louislelay/Experimental-Equipment-for-Orthostatic-Exercise/cad/ガイドローラー.sldasm

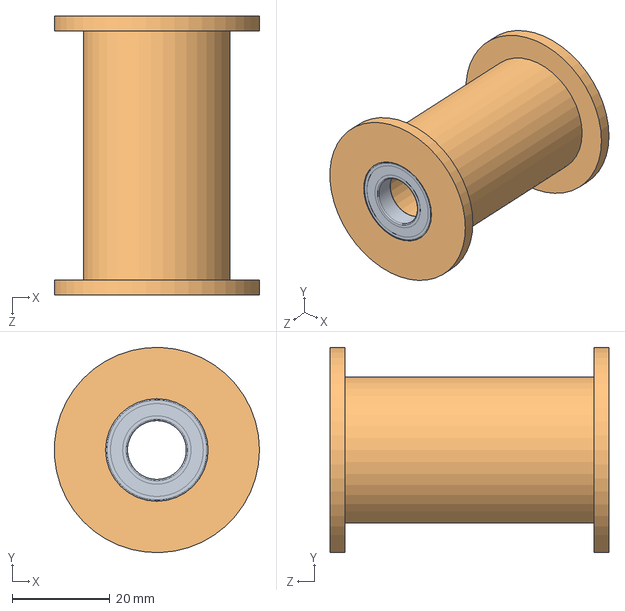
[picture p9: CAD file, 2024-07-01]
cad/ガイドローラー.sldasm
41.9 x 42.0 x 57.0 mm
ガイドローラ_51x30
6801ZZ x 2
