louislelay/Experimental-Equipment-for-Orthostatic-Exercise/cad/ベルト制御ユニット_左.sldasm

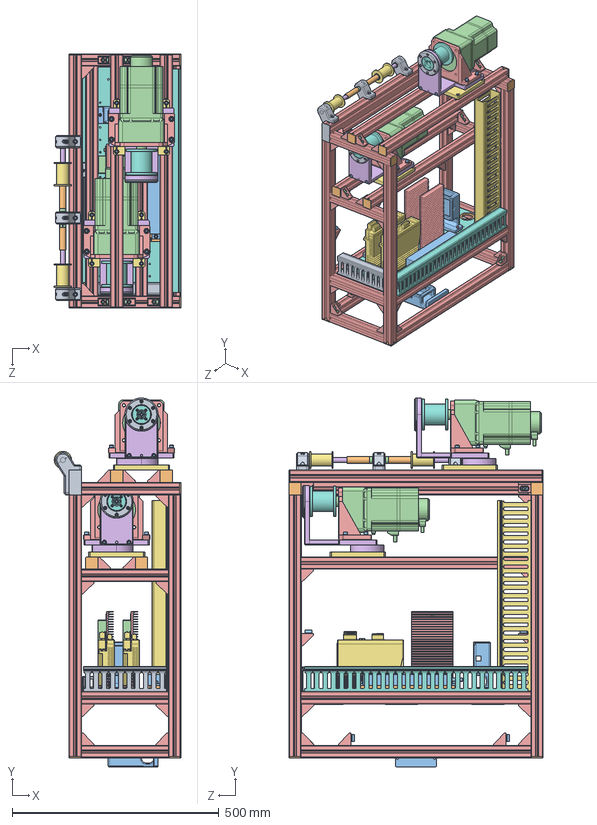
[picture p20: CAD file, 2024-07-01]
cad/ベルト制御ユニット_左.sldasm
306.0 x 892.3 x 615.0 mm
筐体フレーム
配線ダクト用ブラケット x 2
KD-48-20-T
KD-36-20-T
HFC6-3060-B x 2
HFC6-3030-B x 14
HNTP6-6_app x 115
HBLFSN6_CBM6-12 x 98
HBLFSNB6-SEP_b x 49
SFRW12-390-M6-N6_s
ガイドローラ_51x30 x 2
6801ZZ x 4
ガイドローラー用シャフトブラケット x 3
カラー_7 x 2
カラー_30 x 2
カラー_62 x 2
CB6-12 x 29
BXM6200M-10 x 2
SOL6M8 x 2
モーターブラケット x 2
6808ZZ x 2
ベルト巻き取りドラム x 2
ベアリングキャップ x 2
MS6-60 x 2
CB6-20 x 16
WSJ-STN-M6 x 8
CB4-10 x 56
FFS080 v1 x 2
モーターユニット架台プレート x 2
HNTP6-5 x 8
中板
TAP-K4-10用ベース
TAP-K4-10
RGB100 x 2
17F200L100 x 2
抵抗器用ブラケット x 2
BXSD200-A2 x 2
HFB-4001 x 4
KD-36-20-T_200
NAE-032
AIO160802AY-USB用ケース2 x 2
U2H-Z7SBK_用ケース
中板受け用ブラケット x 6
