louislelay/Experimental-Equipment-for-Orthostatic-Exercise/cad/ベルト制御ユニット_右.sldasm

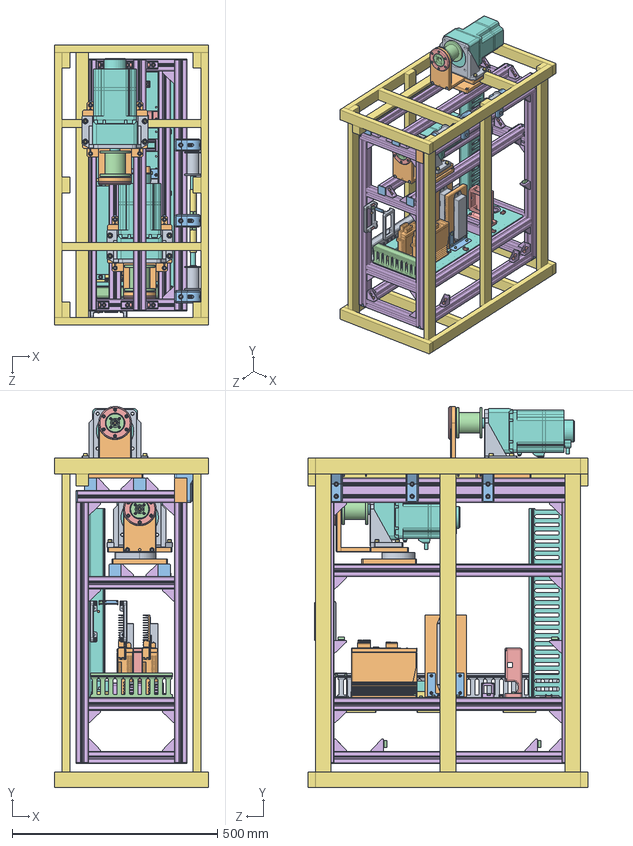
[picture p21: CAD file, 2024-07-01]
cad/ベルト制御ユニット_右.sldasm
376.0 x 928.0 x 683.0 mm
筐体フレーム
配線ダクト用ブラケット x 2
KD-48-20-T
KD-36-20-T
HFC6-3060-B x 2
HFC6-3030-B x 14
HNTP6-6_app x 127
HBLFSN6_CBM6-12 x 98
HBLFSNB6-SEP_b x 49
中板
RGB100 x 2
17F200L100 x 2
抵抗器用ブラケット x 2
CB4-10 x 56
AIO160802AY-USB用ケース2
U2H-Z7SBK_用ケース
TAP-K4-10用ベース
TAP-K4-10
CB6-12 x 41
BXSD200-A2 x 2
HFB-4001 x 4
KD-36-20-T_200
TM2S6-C x 4
NAE-032
中板受け用ブラケット x 6
SFRW12-390-M6-N6_s
ガイドローラ_51x30 x 2
6801ZZ x 4
ガイドローラー用シャフトブラケット x 3
カラー_7 x 2
カラー_2 x 4
カラー_30 x 2
カラー_62 x 2
BXM6200M-10 x 2
SOL6M8 x 2
モーターブラケット x 2
6808ZZ x 2
ベルト巻き取りドラム x 2
ベアリングキャップ x 2
MS6-60 x 2
CB6-20 x 16
WSJ-STN-M6 x 8
FFS080 v1 x 2
モーターユニット架台プレート x 2
HNTP6-5 x 8
ASB-320E x 4
S3B-XH-A
S12B-XH-A
ledverm5mmGa
カバー
