louislelay/Experimental-Equipment-for-Orthostatic-Exercise/cad/USB_IO.SLDASM

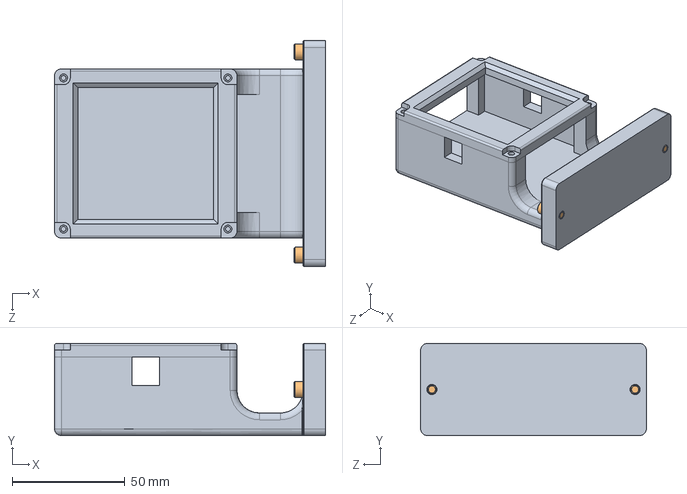
[picture p22: CAD file, 2024-07-01]
cad/USB_IO.SLDASM
120.0 x 40.8 x 100.0 mm
AIO160802AY-USB用ケース2
CB4-10 x 2
