louislelay/Experimental-Equipment-for-Orthostatic-Exercise/cad/hand_protection_pieces/protection hand.SLDPRT

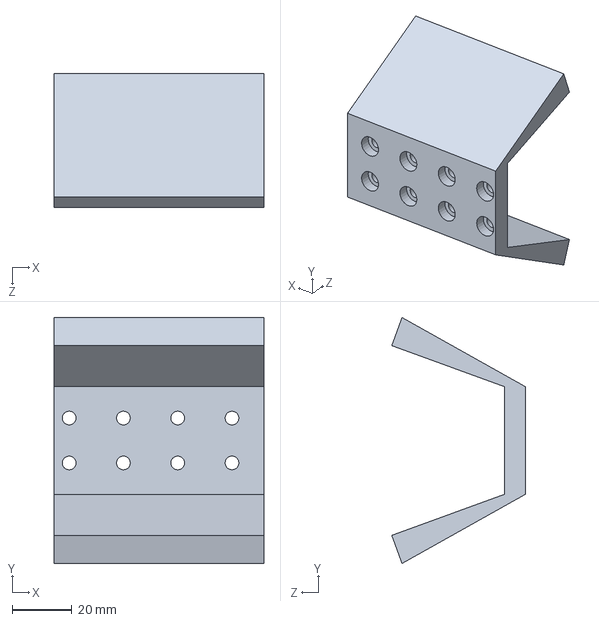
[picture p23: CAD file, 2024-07-02]
cad/hand_protection_pieces/protection hand.SLDPRT
70.0 x 82.2 x 44.6 mm
