louislelay/Experimental-Equipment-for-Orthostatic-Exercise/cad/6808ZZ.SLDPRT

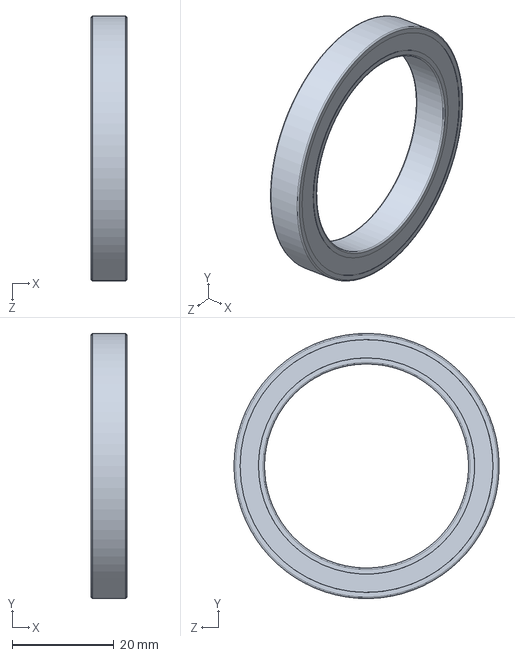
[picture p24: CAD file, 2024-07-01]
cad/6808ZZ.SLDPRT
7.00 x 52.0 x 52.0 mm
