louislelay/Experimental-Equipment-for-Orthostatic-Exercise/cad/hand_protection_pieces/attach_protection.SLDPRT

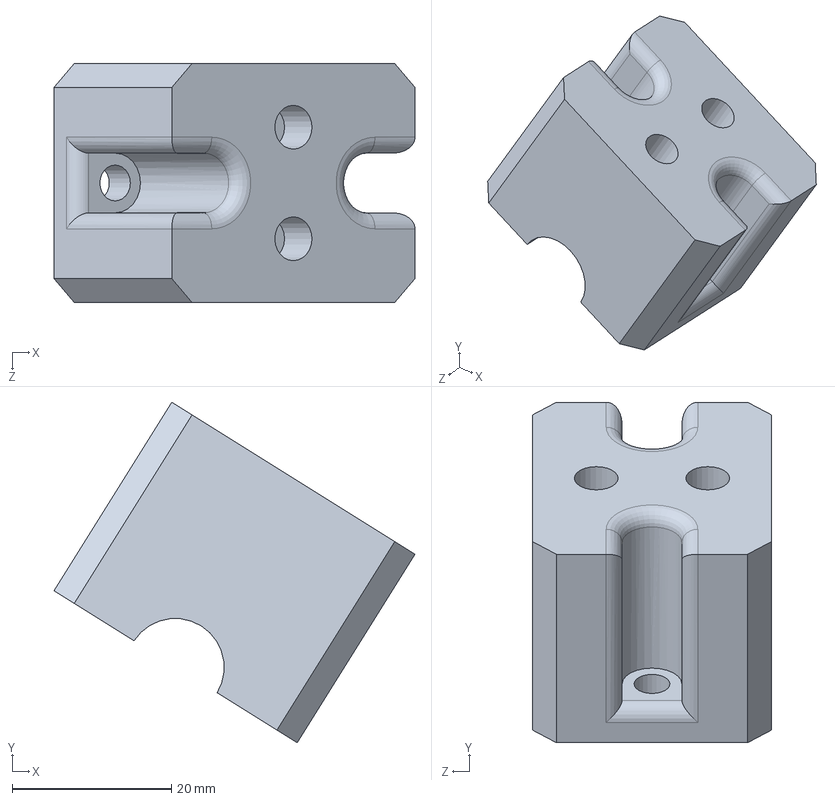
[picture p25: CAD file, 2024-07-01]
cad/hand_protection_pieces/attach_protection.SLDPRT
45.3 x 42.7 x 30.0 mm
