louislelay/Experimental-Equipment-for-Orthostatic-Exercise/cad/hand_protection_pieces/156_protection.SLDPRT

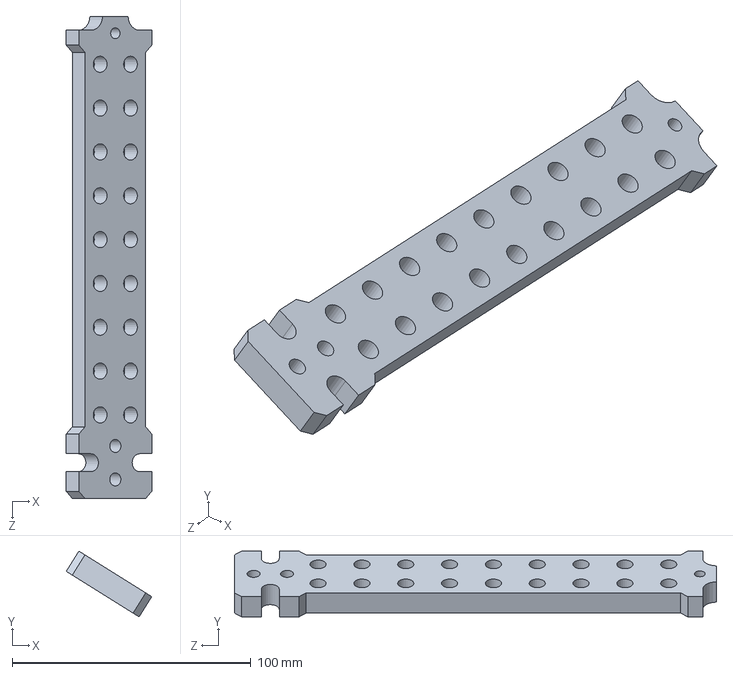
[picture p26: CAD file, 2024-07-01]
cad/hand_protection_pieces/156_protection.SLDPRT
35.8 x 27.6 x 201.8 mm
