louislelay/Experimental-Equipment-for-Orthostatic-Exercise/cad/S3B-XH-A.SLDPRT

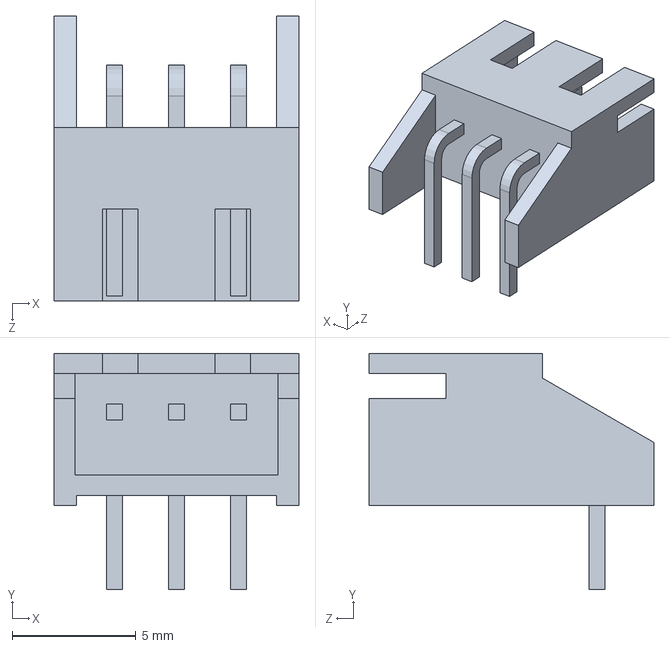
[picture p27: CAD file, 2024-07-01]
cad/S3B-XH-A.SLDPRT
9.90 x 9.55 x 11.5 mm
