louislelay/Experimental-Equipment-for-Orthostatic-Exercise/cad/ledverm5mmGa.SLDPRT

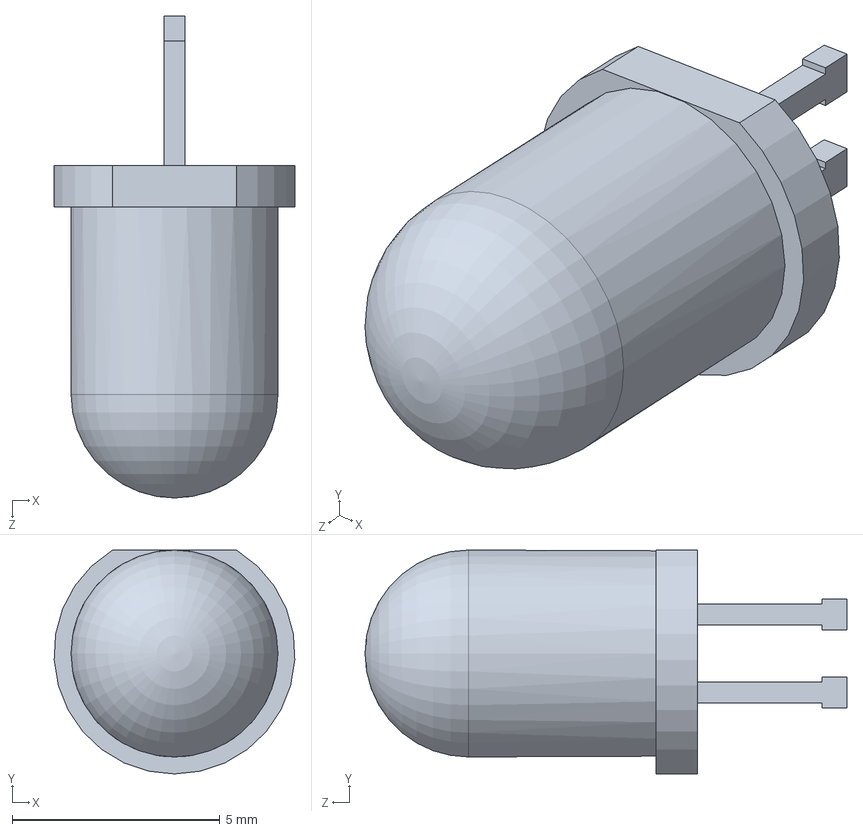
[picture p28: CAD file, 2024-07-01]
cad/ledverm5mmGa.SLDPRT
5.79 x 5.39 x 11.6 mm
