louislelay/Experimental-Equipment-for-Orthostatic-Exercise/cad/ベアリングキャップ.SLDPRT

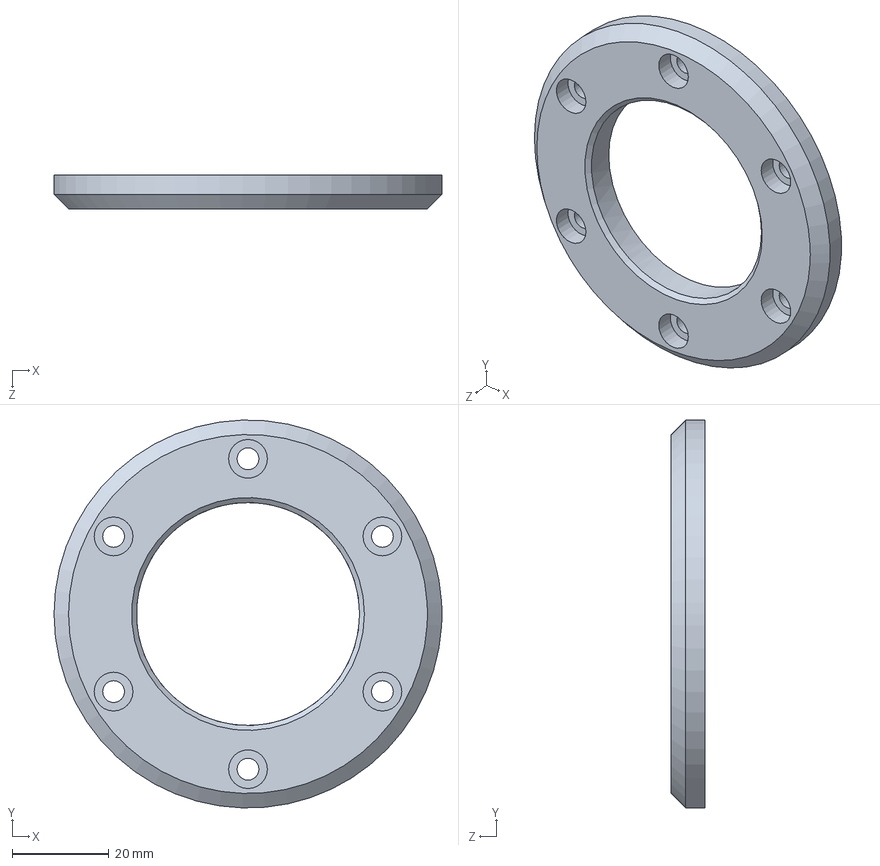
[picture p29: CAD file, 2024-07-01]
cad/ベアリングキャップ.SLDPRT
80.0 x 80.0 x 7.00 mm
