louislelay/Experimental-Equipment-for-Orthostatic-Exercise/cad/6801ZZ.SLDPRT

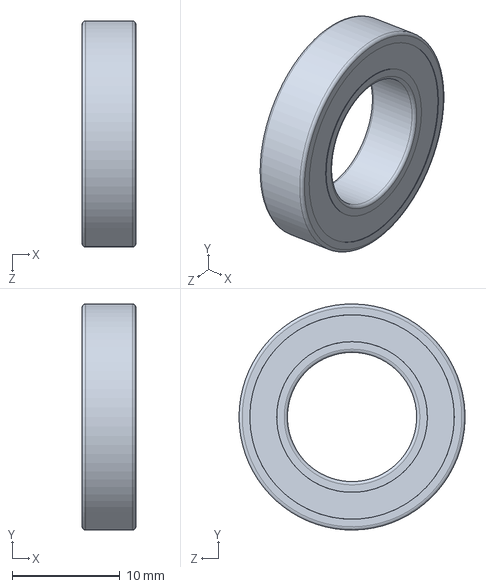
[picture p30: CAD file, 2024-07-01]
cad/6801ZZ.SLDPRT
5.00 x 21.0 x 21.0 mm
