louislelay/Experimental-Equipment-for-Orthostatic-Exercise/cad/NAE-032.SLDPRT

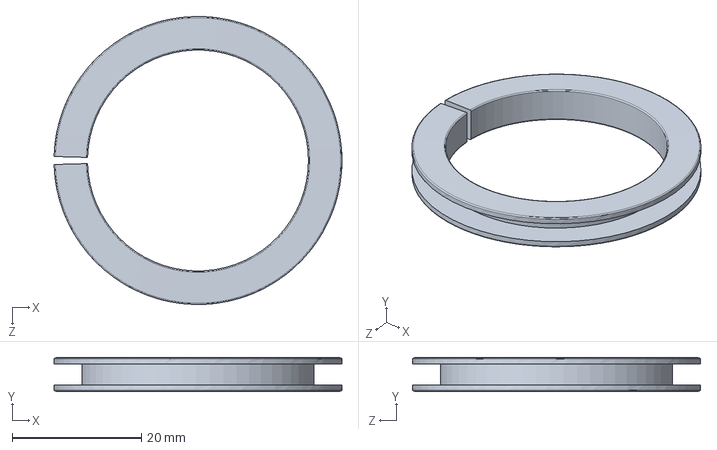
[picture p31: CAD file, 2024-07-01]
cad/NAE-032.SLDPRT
44.6 x 5.30 x 44.6 mm
