louislelay/Experimental-Equipment-for-Orthostatic-Exercise/cad/HNTP6-6_app.sldprt

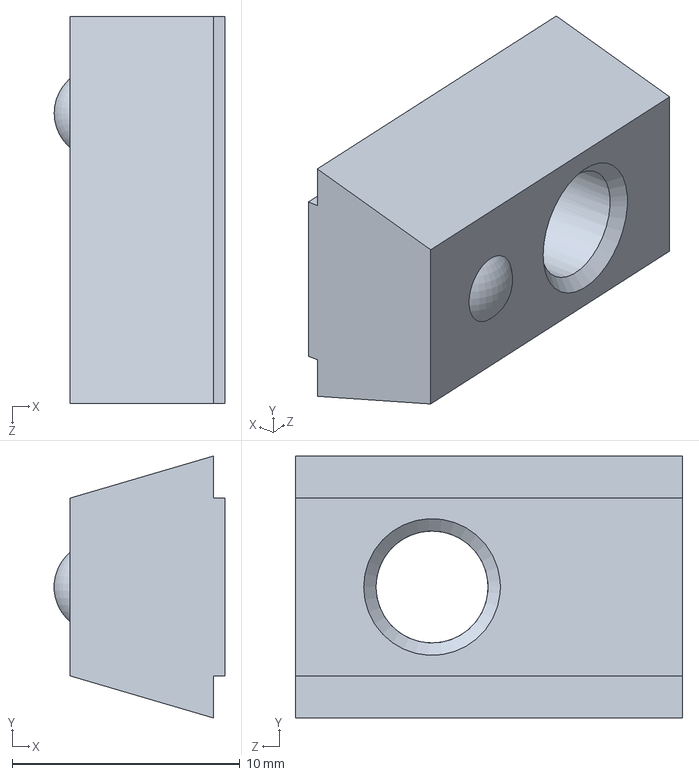
[picture p32: CAD file, 2024-07-01]
cad/HNTP6-6_app.sldprt
7.49 x 11.5 x 17.0 mm
