louislelay/Experimental-Equipment-for-Orthostatic-Exercise/cad/HBLFSN6_CBM6-12.sldprt

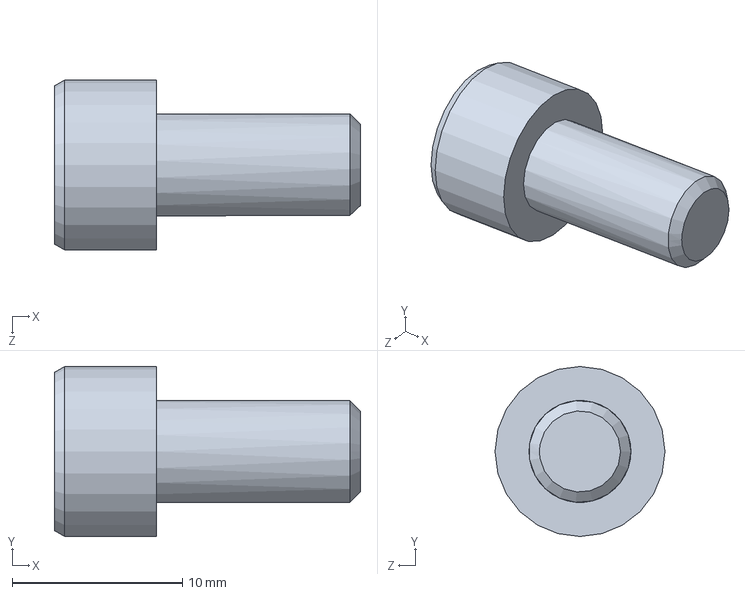
[picture p33: CAD file, 2024-07-01]
cad/HBLFSN6_CBM6-12.sldprt
18.0 x 10.0 x 10.0 mm
