louislelay/Experimental-Equipment-for-Orthostatic-Exercise/cad/ガイドローラー用シャフトブラケット.sldprt

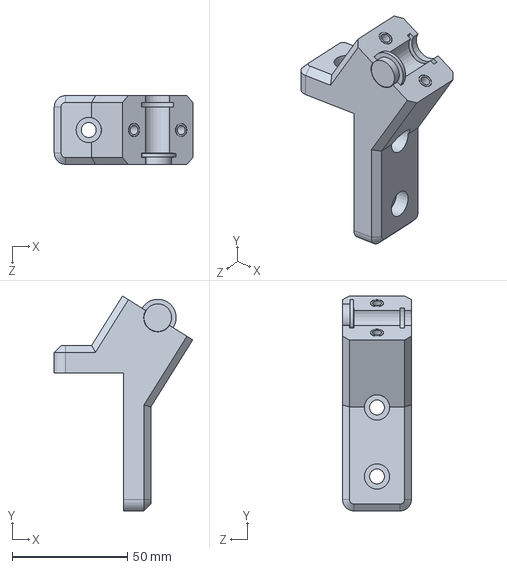
[picture p34: CAD file, 2024-07-01]
cad/ガイドローラー用シャフトブラケット.sldprt
60.2 x 93.5 x 30.0 mm
