louislelay/Experimental-Equipment-for-Orthostatic-Exercise/cad/カラー_62.sldprt

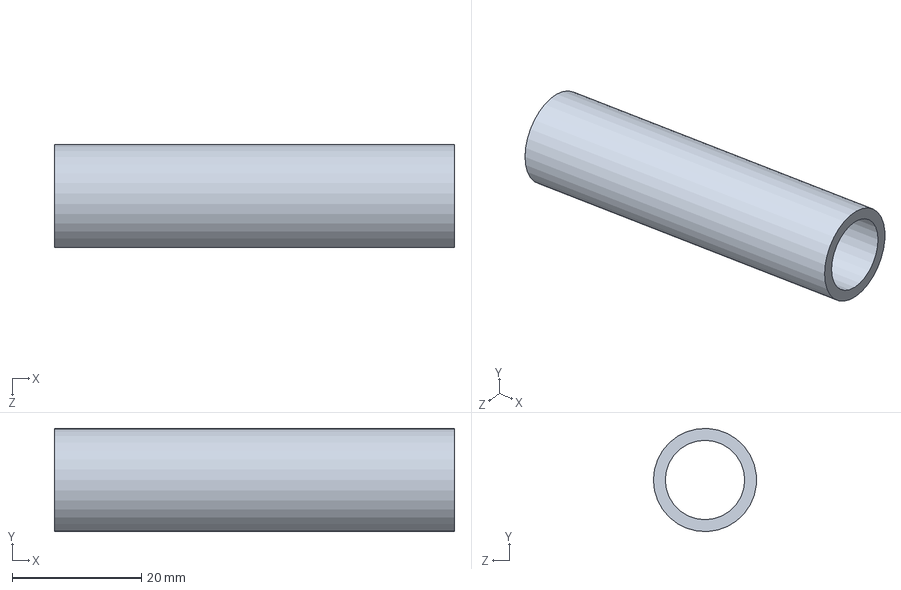
[picture p35: CAD file, 2024-07-01]
cad/カラー_62.sldprt
62.0 x 16.0 x 16.0 mm
