louislelay/Experimental-Equipment-for-Orthostatic-Exercise/cad/ASB-320E.SLDPRT

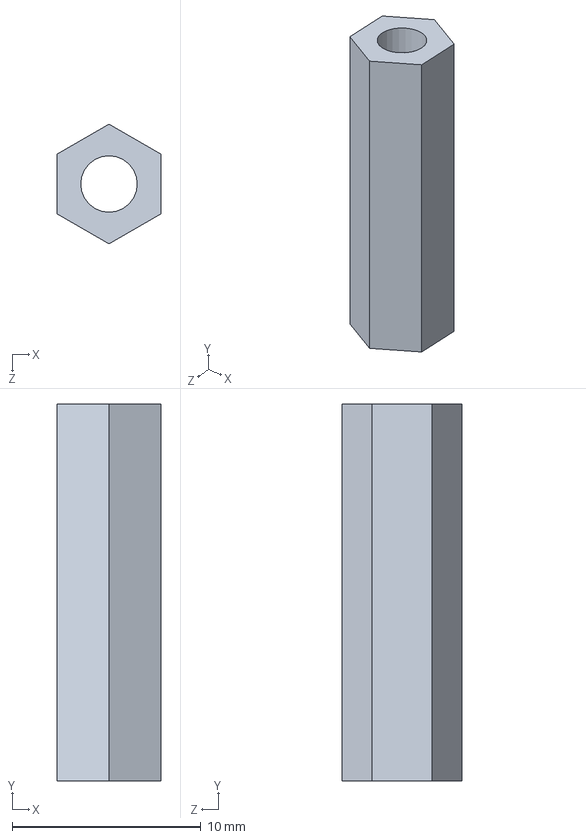
[picture p36: CAD file, 2024-07-01]
cad/ASB-320E.SLDPRT
5.50 x 20.0 x 6.35 mm
