louislelay/Experimental-Equipment-for-Orthostatic-Exercise/cad/BXSD200-A2.sldprt

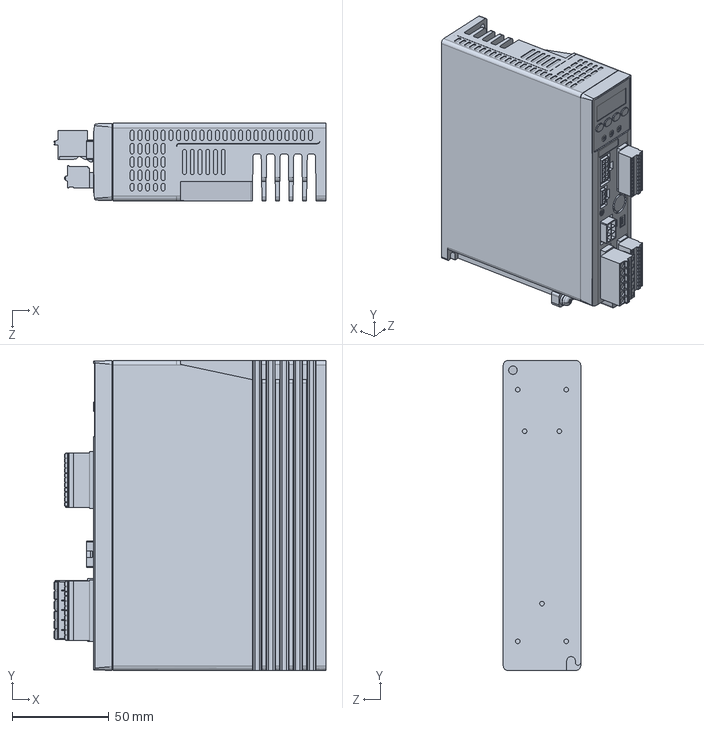
[picture p37: CAD file, 2024-07-01]
cad/BXSD200-A2.sldprt
140.3 x 160.0 x 40.0 mm
