louislelay/Experimental-Equipment-for-Orthostatic-Exercise/cad/中板受け用ブラケット.sldprt

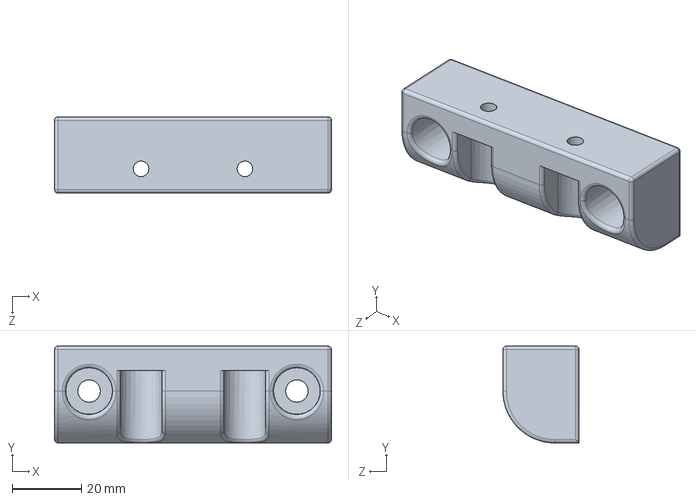
[picture p38: CAD file, 2024-07-01]
cad/中板受け用ブラケット.sldprt
80.0 x 28.0 x 22.0 mm
