louislelay/Experimental-Equipment-for-Orthostatic-Exercise/cad/17F200L100.SLDPRT

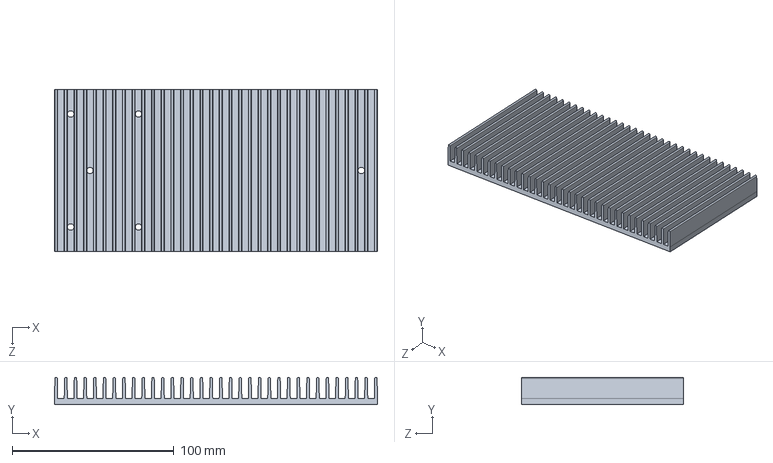
[picture p39: CAD file, 2024-07-01]
cad/17F200L100.SLDPRT
200.0 x 17.0 x 100.0 mm
