louislelay/Experimental-Equipment-for-Orthostatic-Exercise/cad/U2H-Z7SBK_用ケース.SLDPRT

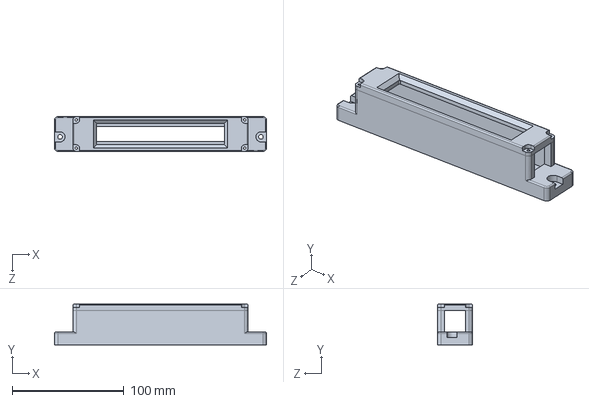
[picture p40: CAD file, 2024-07-01]
cad/U2H-Z7SBK_用ケース.SLDPRT
190.0 x 36.7 x 31.2 mm
