louislelay/Experimental-Equipment-for-Orthostatic-Exercise/cad/HBLFSNB6-SEP_b.sldprt

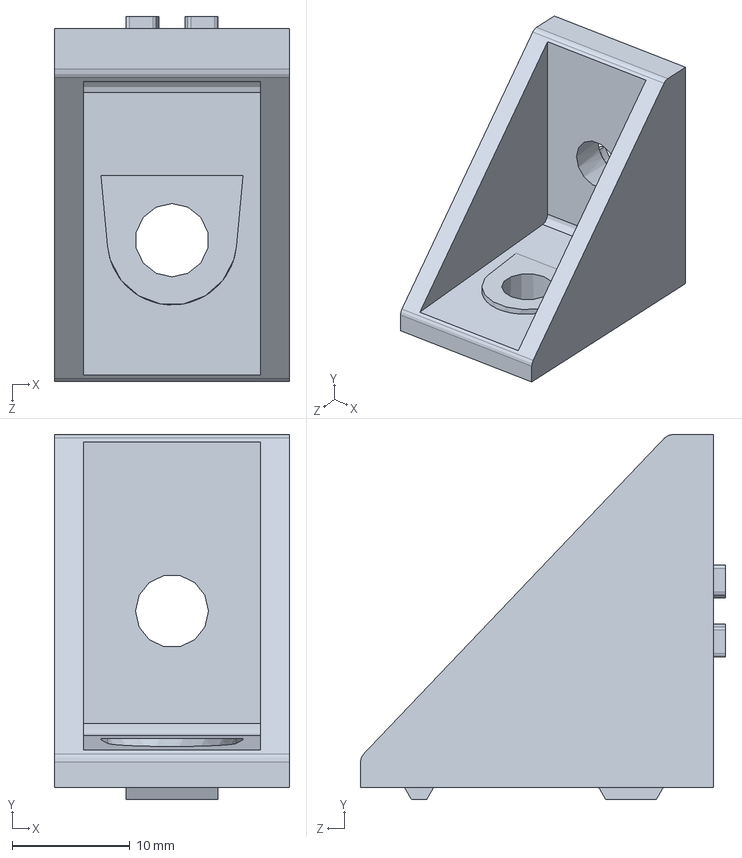
[picture p41: CAD file, 2024-07-01]
cad/HBLFSNB6-SEP_b.sldprt
20.0 x 31.0 x 31.0 mm
