louislelay/Experimental-Equipment-for-Orthostatic-Exercise/cad/カバー.SLDPRT

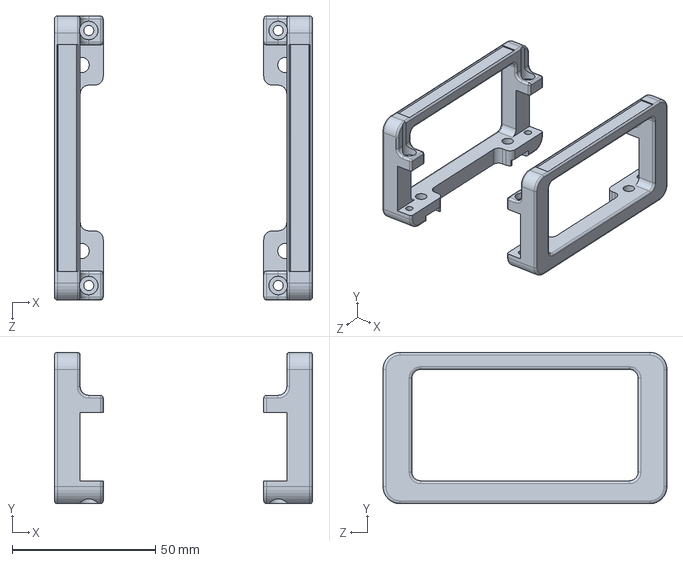
[picture p42: CAD file, 2024-07-01]
cad/カバー.SLDPRT
90.0 x 52.8 x 99.0 mm
