louislelay/Experimental-Equipment-for-Orthostatic-Exercise/cad/カラー_7.sldprt

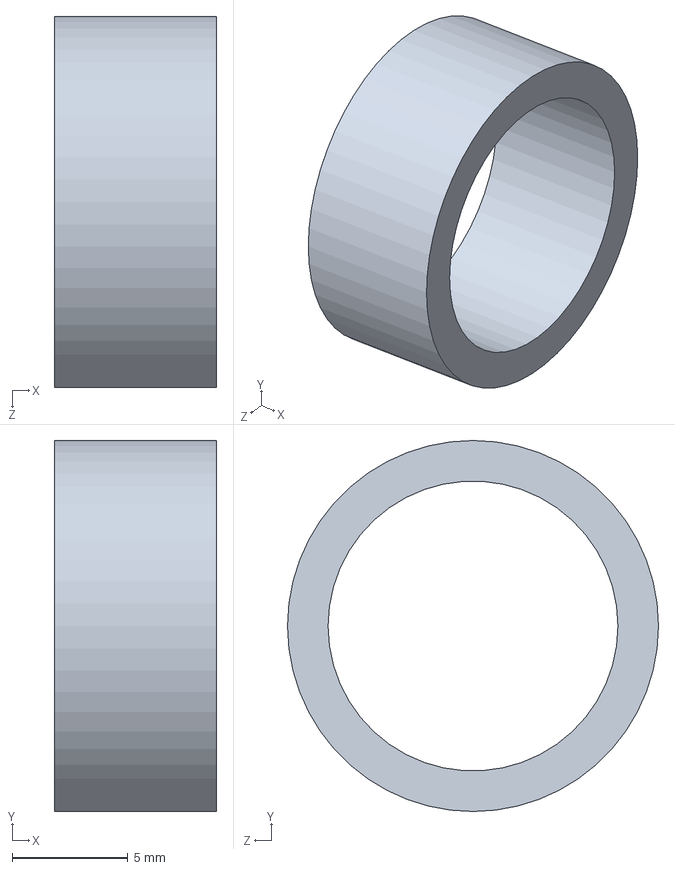
[picture p43: CAD file, 2024-07-01]
cad/カラー_7.sldprt
7.00 x 16.0 x 16.0 mm
