louislelay/Experimental-Equipment-for-Orthostatic-Exercise/cad/HFC6-3060-B.sldprt

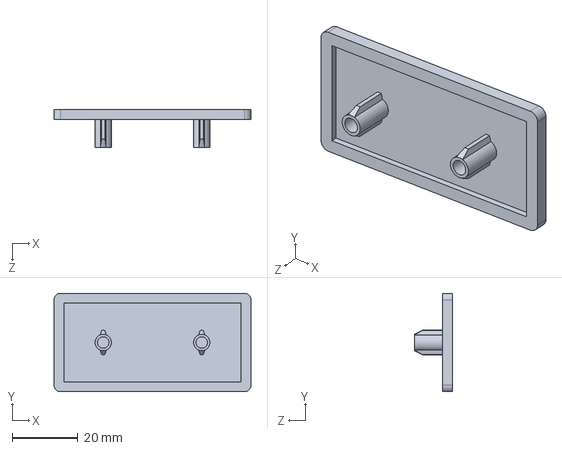
[picture p44: CAD file, 2024-07-01]
cad/HFC6-3060-B.sldprt
60.0 x 30.0 x 11.5 mm
