louislelay/Experimental-Equipment-for-Orthostatic-Exercise/cad/TM2S6-C.SLDPRT

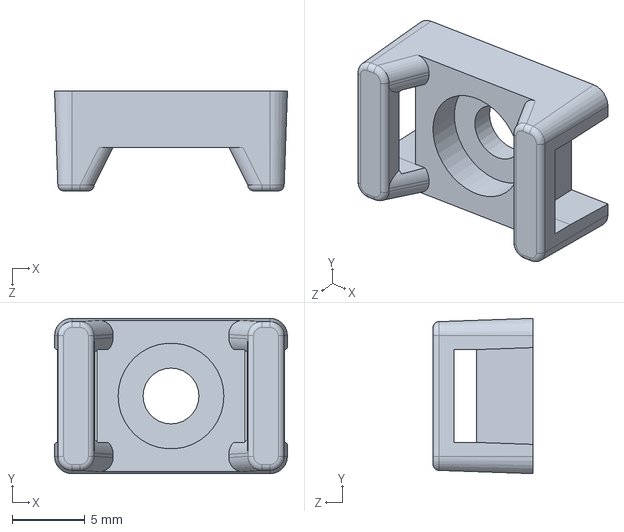
[picture p45: CAD file, 2024-07-01]
cad/TM2S6-C.SLDPRT
16.0 x 10.7 x 6.86 mm
