louislelay/Experimental-Equipment-for-Orthostatic-Exercise/cad/CB4-10.sldprt

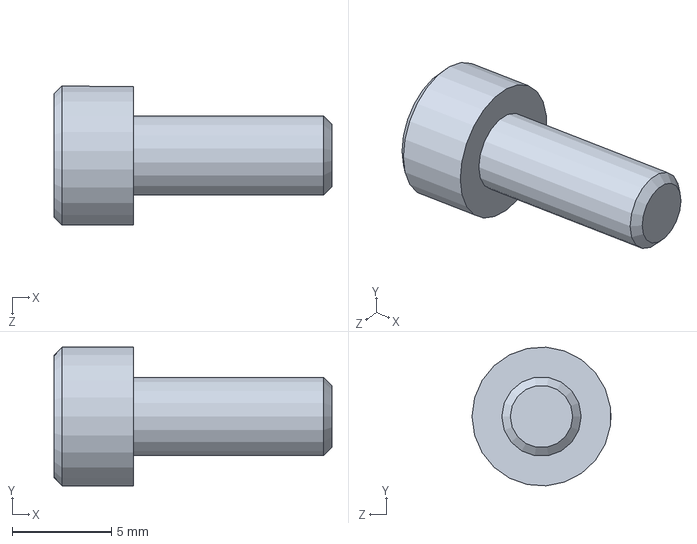
[picture p46: CAD file, 2024-07-01]
cad/CB4-10.sldprt
14.0 x 6.98 x 7.00 mm
