louislelay/Experimental-Equipment-for-Orthostatic-Exercise/cad/モーターブラケット.SLDPRT

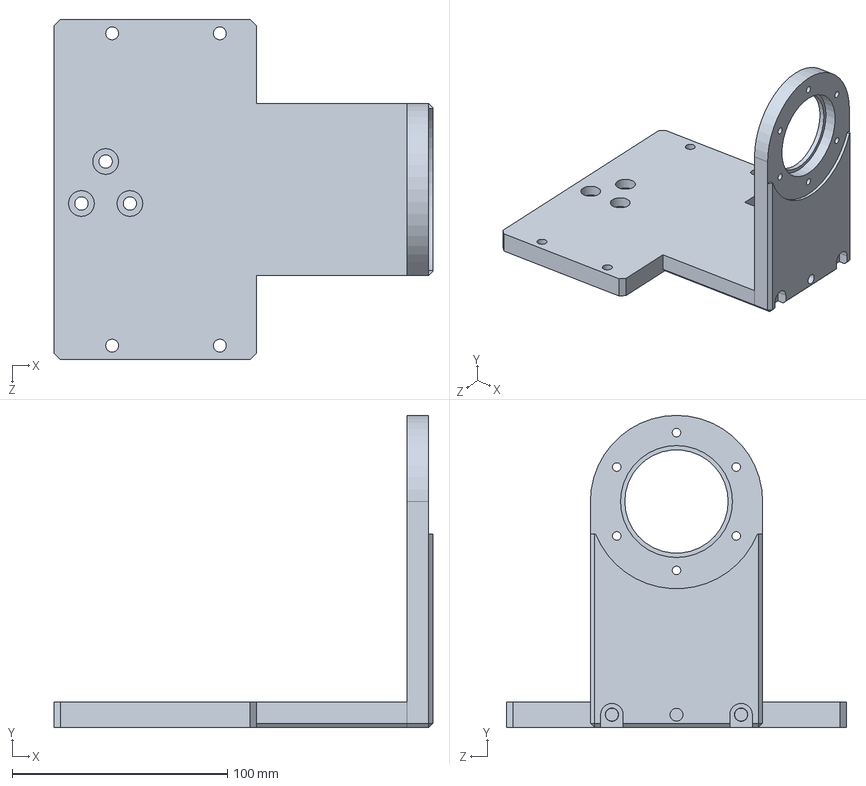
[picture p47: CAD file, 2024-07-01]
cad/モーターブラケット.SLDPRT
176.0 x 145.0 x 158.0 mm
