louislelay/Experimental-Equipment-for-Orthostatic-Exercise/cad/SFRW12-390-M6-N6_s.sldprt

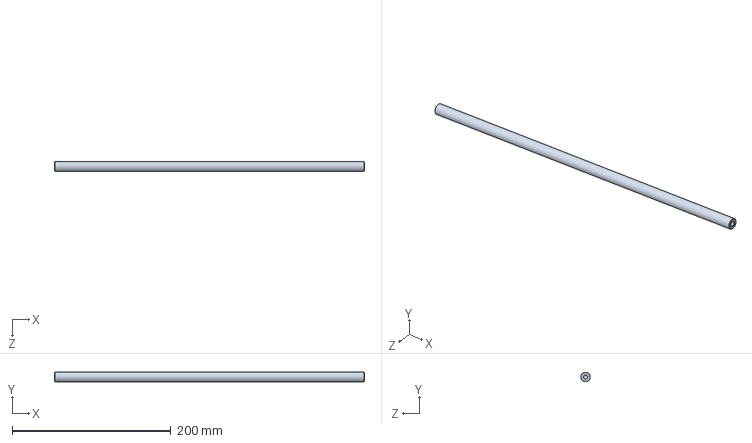
[picture p48: CAD file, 2024-07-01]
cad/SFRW12-390-M6-N6_s.sldprt
390.0 x 12.0 x 12.0 mm
