louislelay/Experimental-Equipment-for-Orthostatic-Exercise/cad/RGB100.SLDPRT

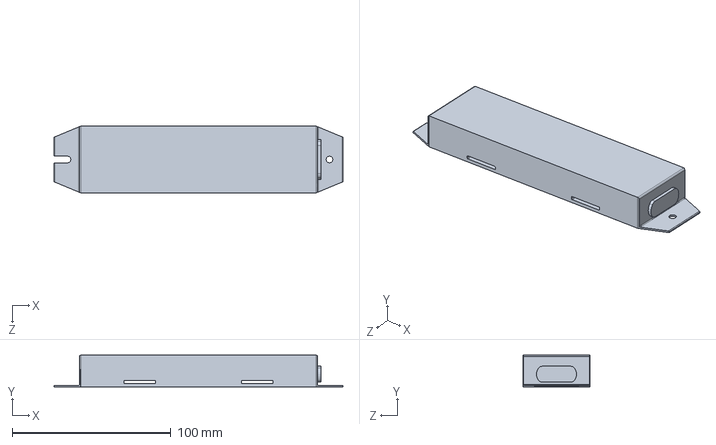
[picture p49: CAD file, 2024-07-01]
cad/RGB100.SLDPRT
182.0 x 20.0 x 42.0 mm
