louislelay/Experimental-Equipment-for-Orthostatic-Exercise/cad/S12B-XH-A.SLDPRT

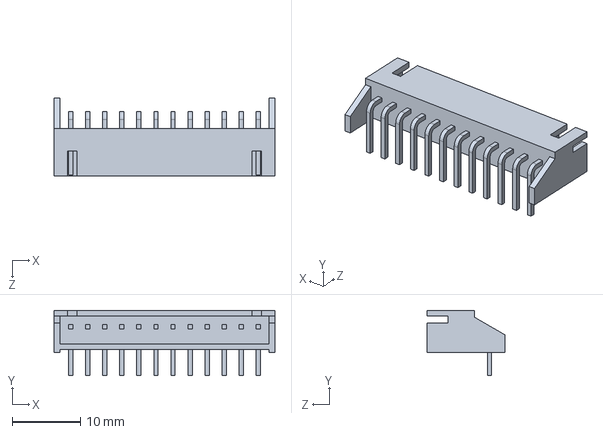
[picture p50: CAD file, 2024-07-01]
cad/S12B-XH-A.SLDPRT
32.4 x 9.55 x 11.5 mm
