louislelay/Experimental-Equipment-for-Orthostatic-Exercise/cad/HFC6-3030-B.sldprt

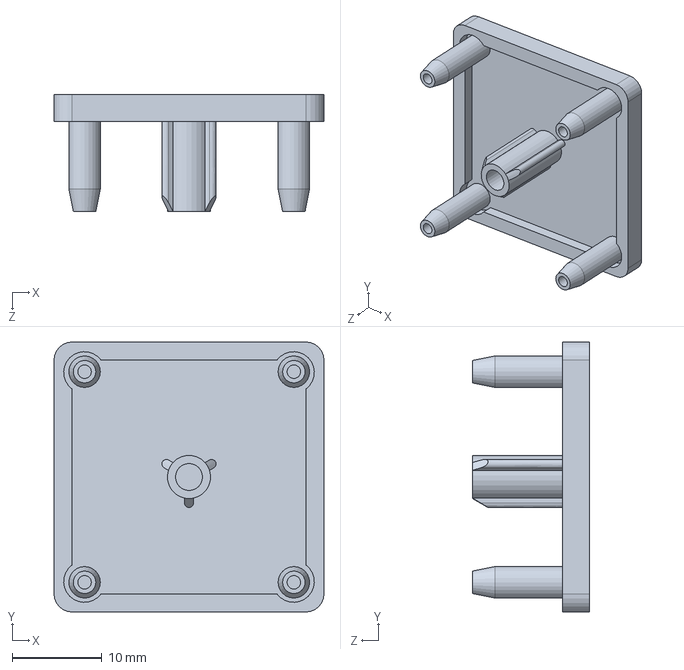
[picture p51: CAD file, 2024-07-01]
cad/HFC6-3030-B.sldprt
30.0 x 30.0 x 13.0 mm
