louislelay/Experimental-Equipment-for-Orthostatic-Exercise/cad/WSJ-STN-M6.SLDPRT

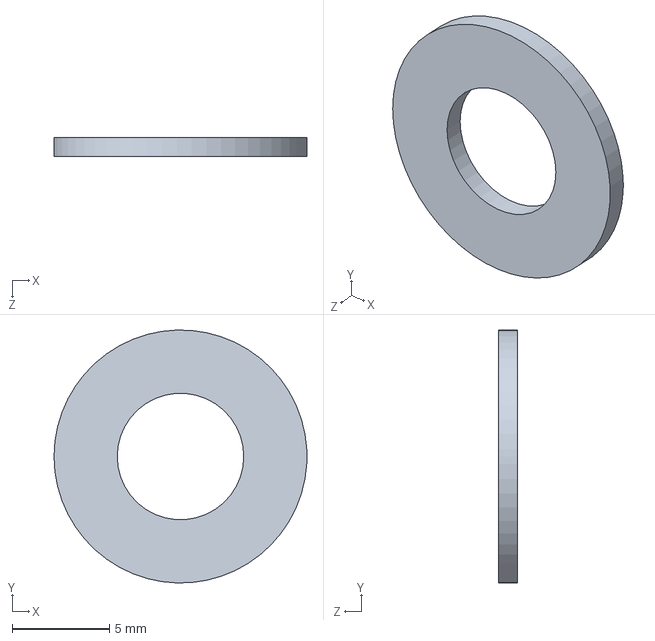
[picture p52: CAD file, 2024-07-01]
cad/WSJ-STN-M6.SLDPRT
13.0 x 13.0 x 1.00 mm
