louislelay/Experimental-Equipment-for-Orthostatic-Exercise/cad/ガイドローラ_51x30.SLDPRT

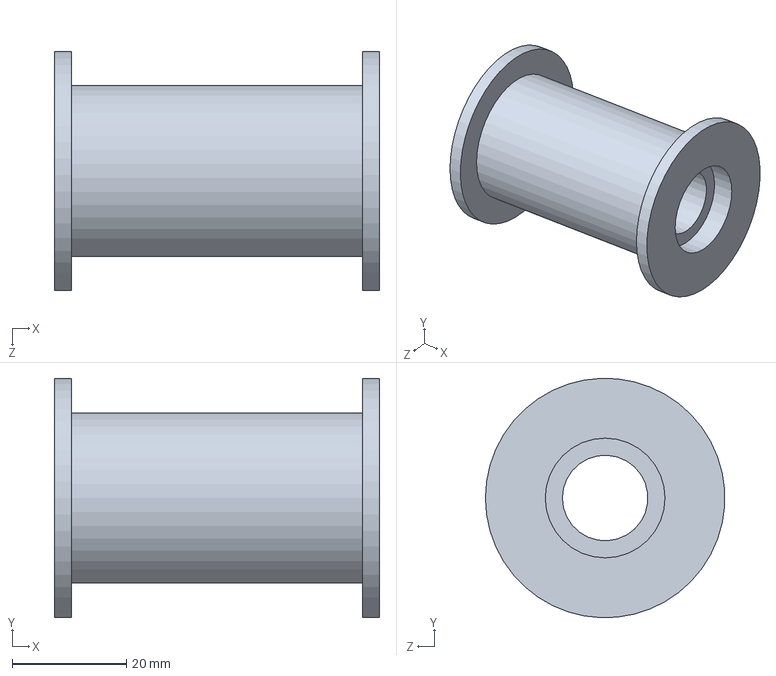
[picture p53: CAD file, 2024-07-01]
cad/ガイドローラ_51x30.SLDPRT
57.0 x 42.0 x 41.9 mm
