louislelay/Experimental-Equipment-for-Orthostatic-Exercise/cad/KD-36-20-T.SLDPRT

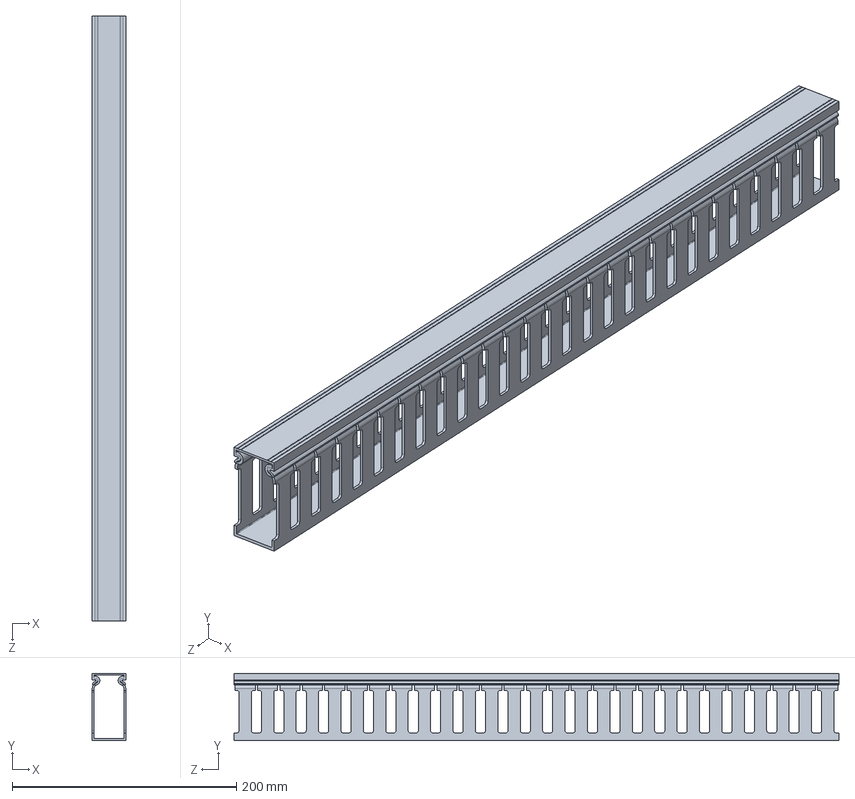
[picture p54: CAD file, 2024-07-01]
cad/KD-36-20-T.SLDPRT
30.0 x 60.2 x 540.0 mm
