louislelay/Experimental-Equipment-for-Orthostatic-Exercise/cad/KD-36-20-T_200.SLDPRT

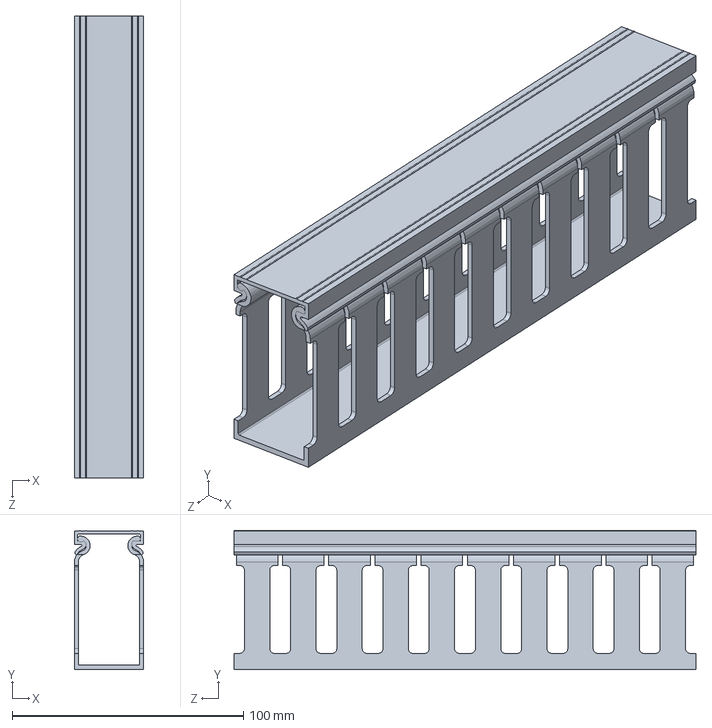
[picture p55: CAD file, 2024-07-01]
cad/KD-36-20-T_200.SLDPRT
30.0 x 60.2 x 200.0 mm
