louislelay/Experimental-Equipment-for-Orthostatic-Exercise/cad/ベルト巻き取りドラム.SLDPRT

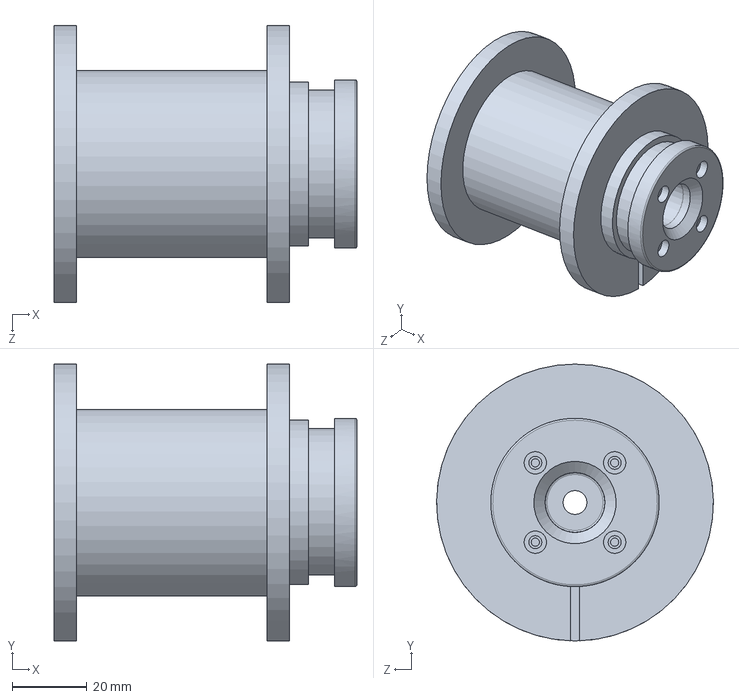
[picture p56: CAD file, 2024-07-01]
cad/ベルト巻き取りドラム.SLDPRT
81.0 x 74.0 x 74.0 mm
