louislelay/Experimental-Equipment-for-Orthostatic-Exercise/cad/MS6-60.SLDPRT

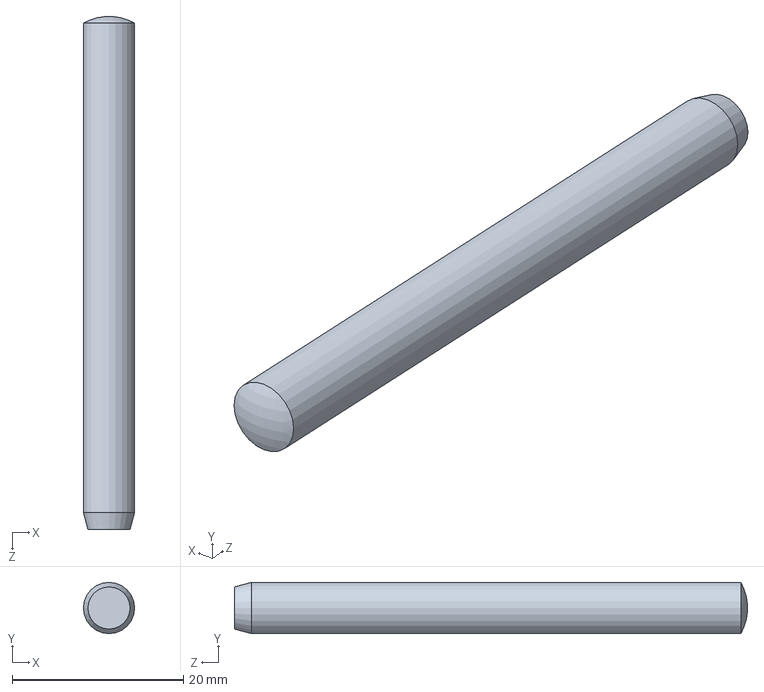
[picture p57: CAD file, 2024-07-01]
cad/MS6-60.SLDPRT
6.00 x 6.00 x 60.0 mm
