louislelay/Experimental-Equipment-for-Orthostatic-Exercise/cad/HNTP6-5.sldprt

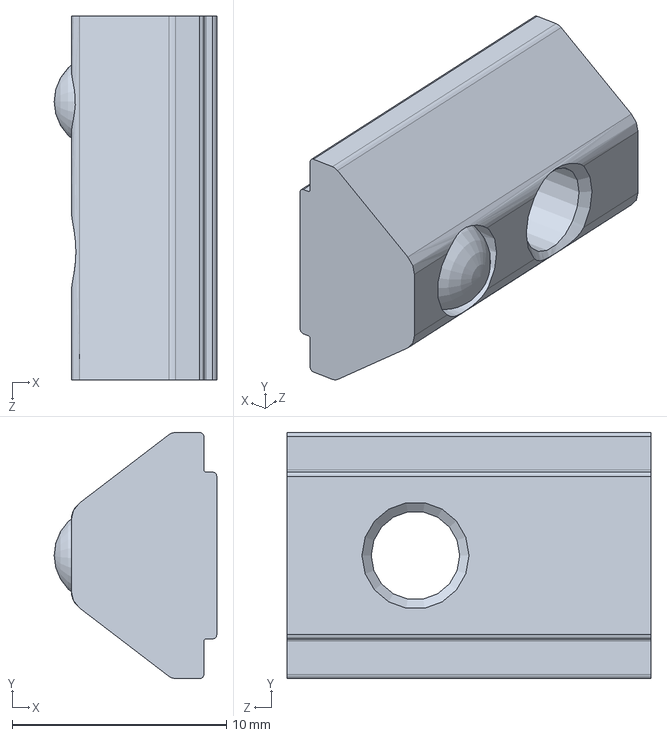
[picture p58: CAD file, 2024-07-01]
cad/HNTP6-5.sldprt
7.60 x 11.5 x 17.0 mm
