louislelay/Experimental-Equipment-for-Orthostatic-Exercise/cad/カラー_30.sldprt

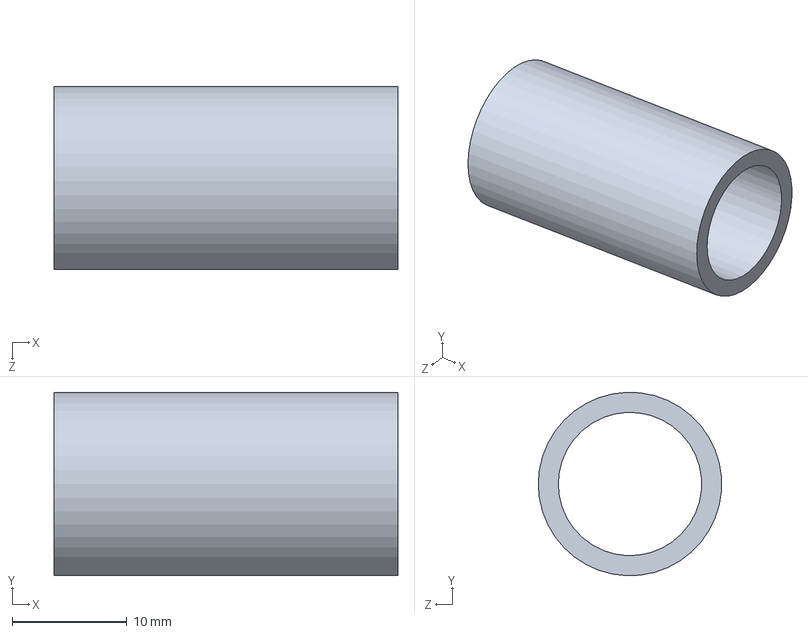
[picture p59: CAD file, 2024-07-01]
cad/カラー_30.sldprt
30.0 x 16.0 x 16.0 mm
