louislelay/Experimental-Equipment-for-Orthostatic-Exercise/cad/FFS080 v1.SLDPRT

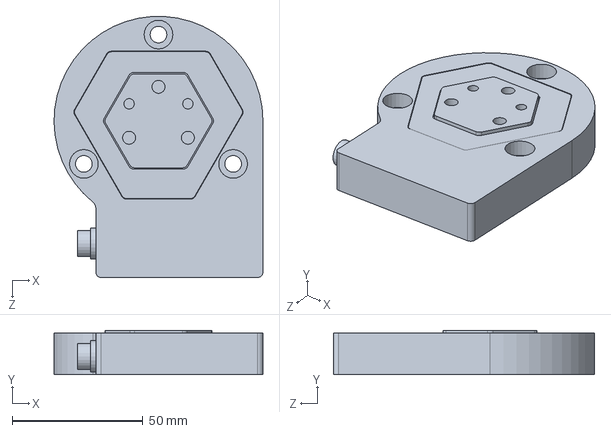
[picture p60: CAD file, 2024-07-01]
cad/FFS080 v1.SLDPRT
80.0 x 17.0 x 99.9 mm
