louislelay/Experimental-Equipment-for-Orthostatic-Exercise/cad/カラー_2.sldprt

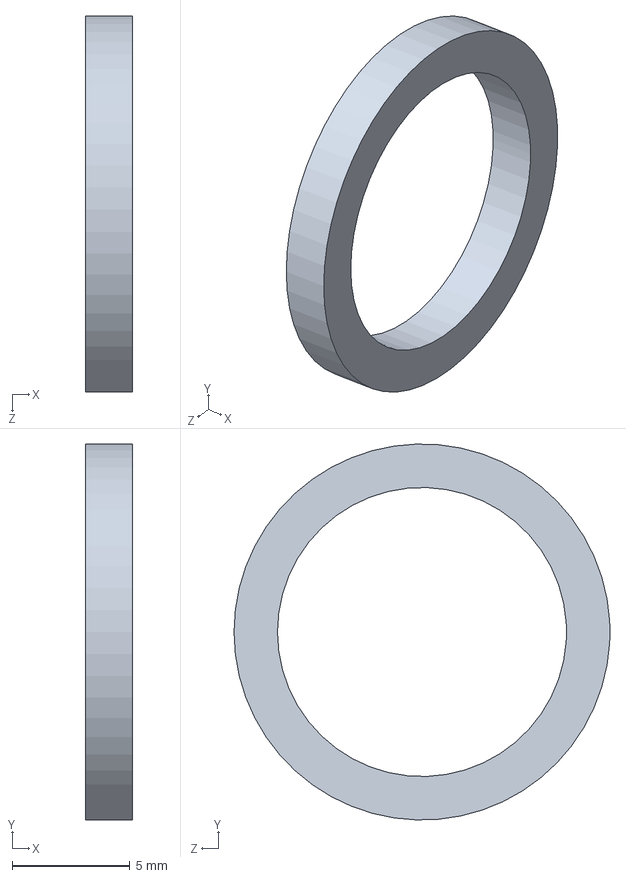
[picture p61: CAD file, 2024-07-01]
cad/カラー_2.sldprt
2.00 x 16.0 x 16.0 mm
