louislelay/Experimental-Equipment-for-Orthostatic-Exercise/cad/配線ダクト用ブラケット.sldprt

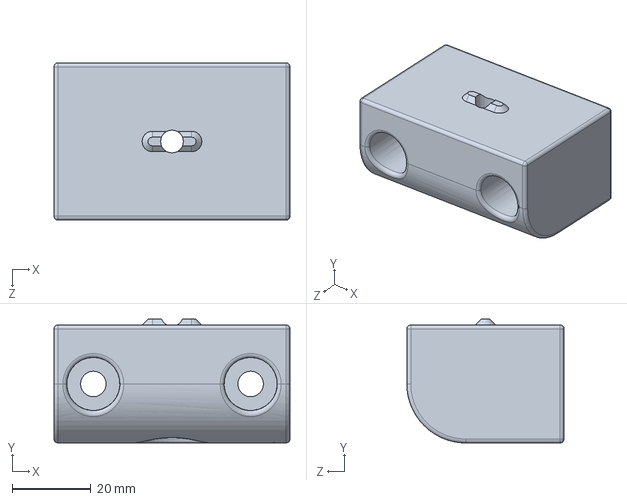
[picture p62: CAD file, 2024-07-01]
cad/配線ダクト用ブラケット.sldprt
60.0 x 31.5 x 40.0 mm
