louislelay/Experimental-Equipment-for-Orthostatic-Exercise/cad/BXM6200M-10.SLDPRT

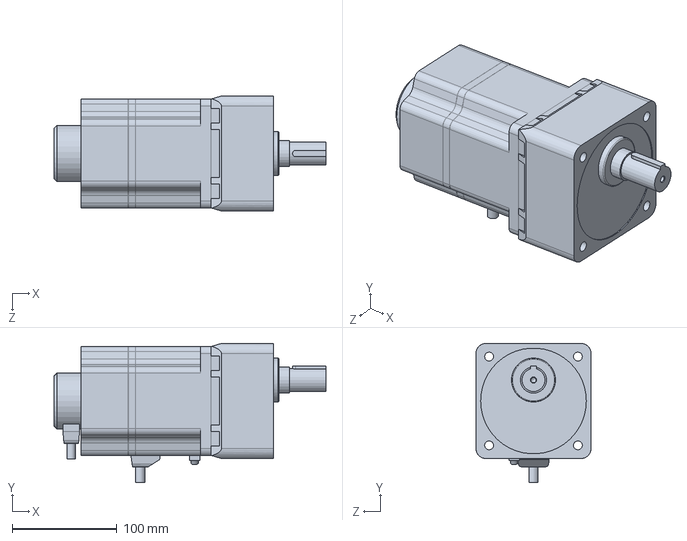
[picture p63: CAD file, 2024-07-01]
cad/BXM6200M-10.SLDPRT
260.0 x 133.0 x 110.0 mm
