louislelay/Experimental-Equipment-for-Orthostatic-Exercise/cad/HFB-4001.SLDPRT

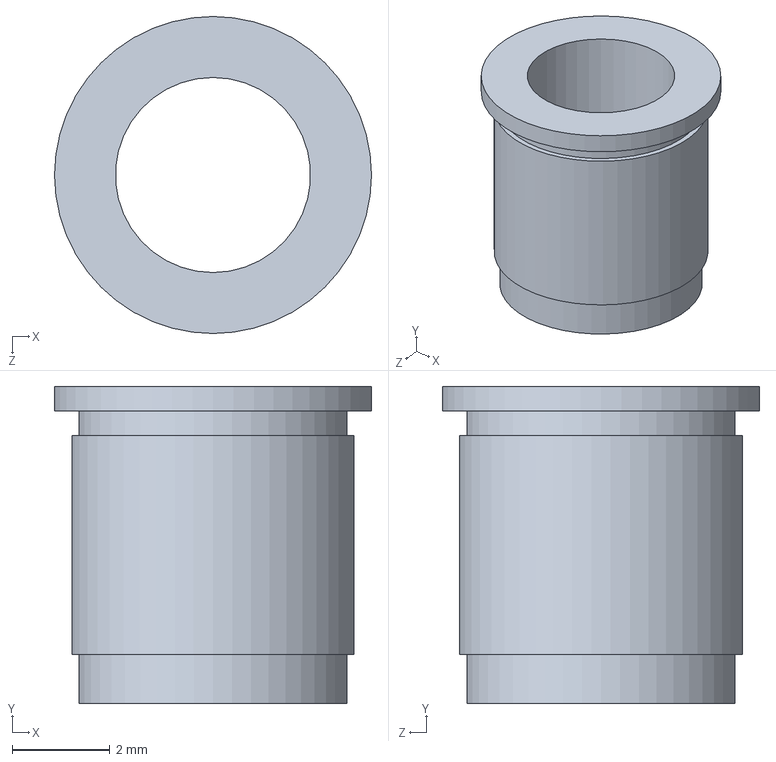
[picture p64: CAD file, 2024-07-01]
cad/HFB-4001.SLDPRT
6.50 x 6.50 x 6.50 mm
