louislelay/Experimental-Equipment-for-Orthostatic-Exercise/cad/SW3dPS-Potentiometer.SLDPRT

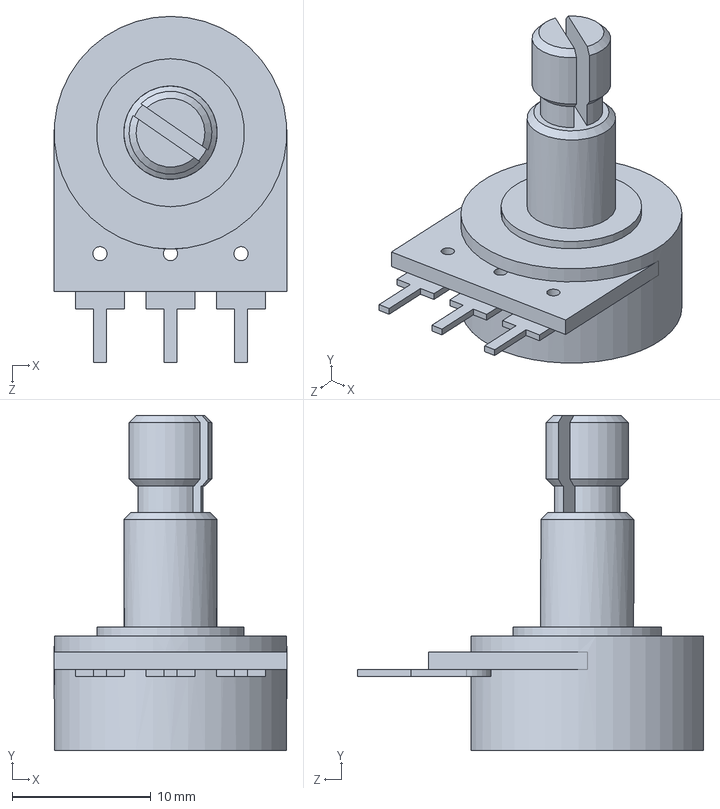
[picture p65: CAD file, 2024-07-01]
cad/SW3dPS-Potentiometer.SLDPRT
16.8 x 24.1 x 24.9 mm
