louislelay/Experimental-Equipment-for-Orthostatic-Exercise/cad/背もたれフレーム用カバー.SLDPRT

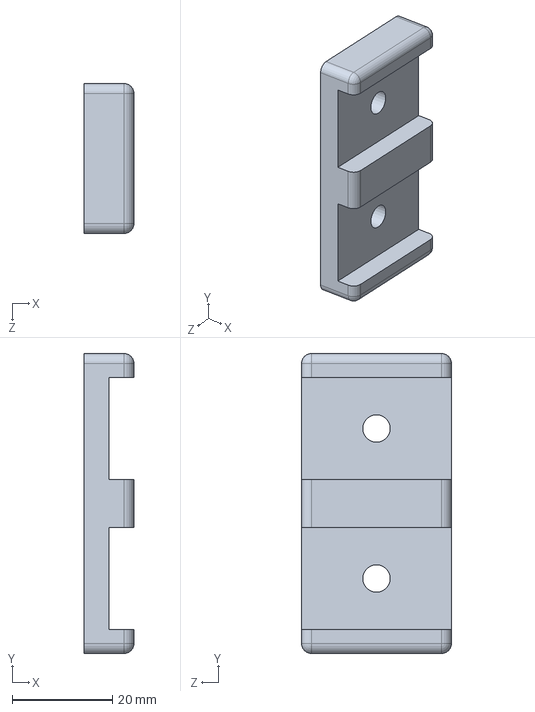
[picture p66: CAD file, 2024-07-01]
cad/背もたれフレーム用カバー.SLDPRT
10.0 x 60.0 x 30.0 mm
