louislelay/Experimental-Equipment-for-Orthostatic-Exercise/cad/CB5-14.sldprt

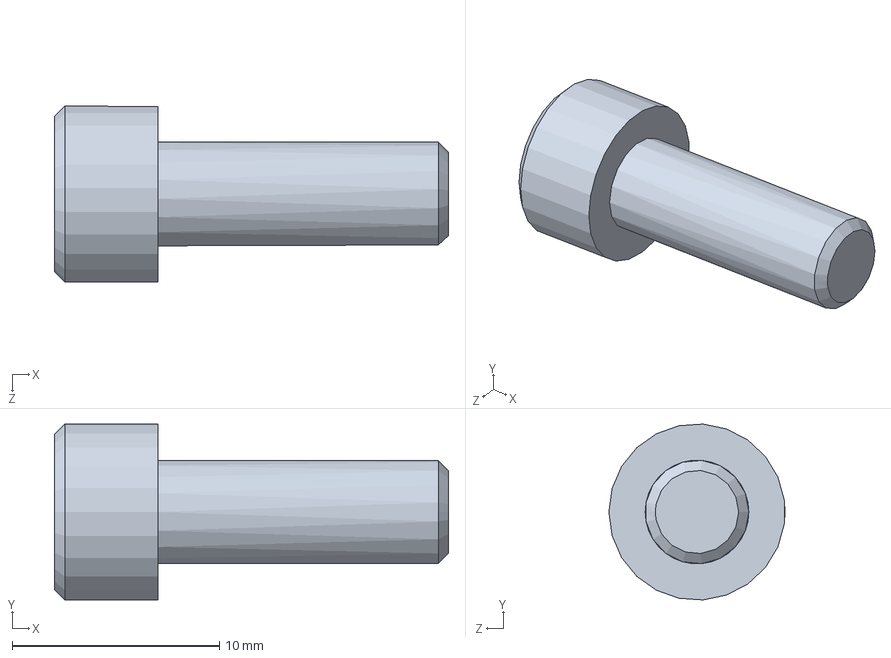
[picture p67: CAD file, 2024-07-01]
cad/CB5-14.sldprt
19.0 x 8.48 x 8.50 mm
