louislelay/Experimental-Equipment-for-Orthostatic-Exercise/cad/連結フレーム.sldprt

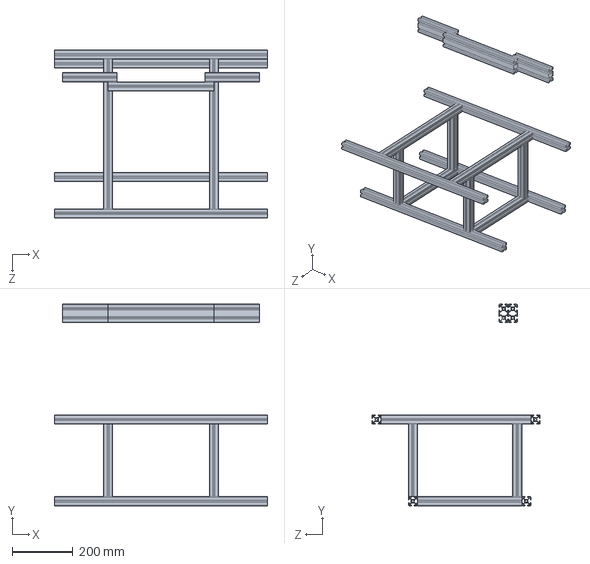
[picture p68: CAD file, 2024-07-01]
cad/連結フレーム.sldprt
704.0 x 666.0 x 555.0 mm
