louislelay/Experimental-Equipment-for-Orthostatic-Exercise/cad/SOL6M8.sldprt

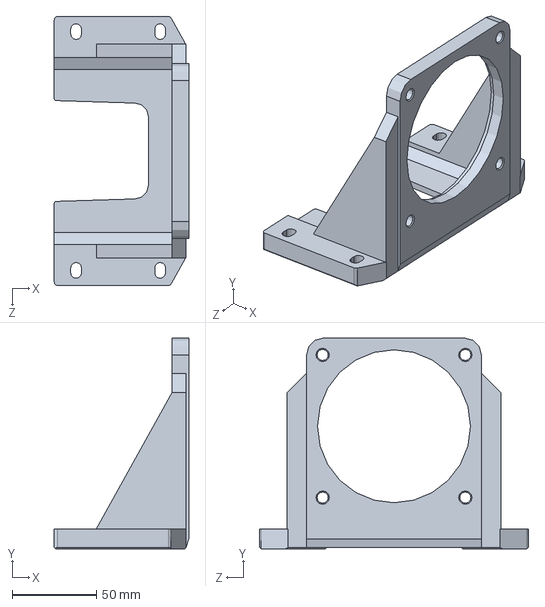
[picture p69: CAD file, 2024-07-01]
cad/SOL6M8.sldprt
80.0 x 125.5 x 160.0 mm
