louislelay/Experimental-Equipment-for-Orthostatic-Exercise/cad/User Library-7101SYZQE_switch-toggle.SLDPRT

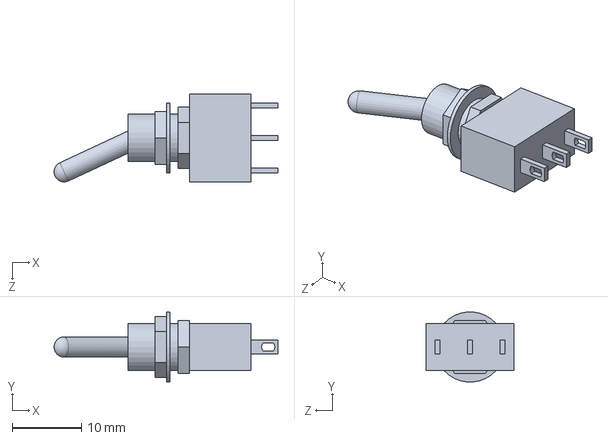
[picture p70: CAD file, 2024-07-01]
cad/User Library-7101SYZQE_switch-toggle.SLDPRT
32.4 x 10.1 x 12.7 mm
