louislelay/Experimental-Equipment-for-Orthostatic-Exercise/cad/抵抗器用ブラケット.SLDPRT

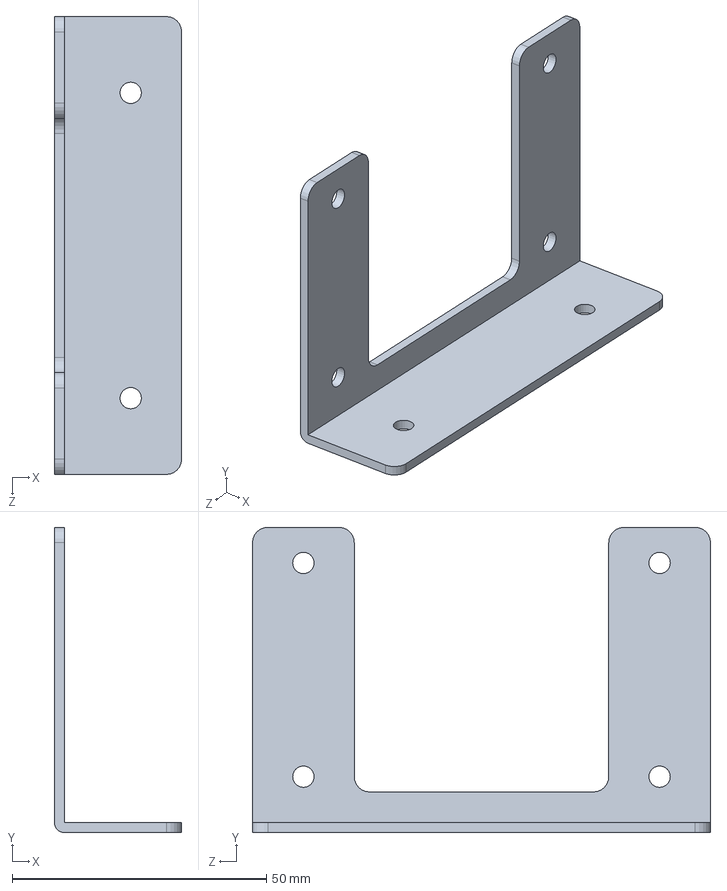
[picture p71: CAD file, 2024-07-01]
cad/抵抗器用ブラケット.SLDPRT
25.0 x 60.0 x 90.0 mm
