louislelay/Experimental-Equipment-for-Orthostatic-Exercise/cad/モーターユニット架台プレート.SLDPRT

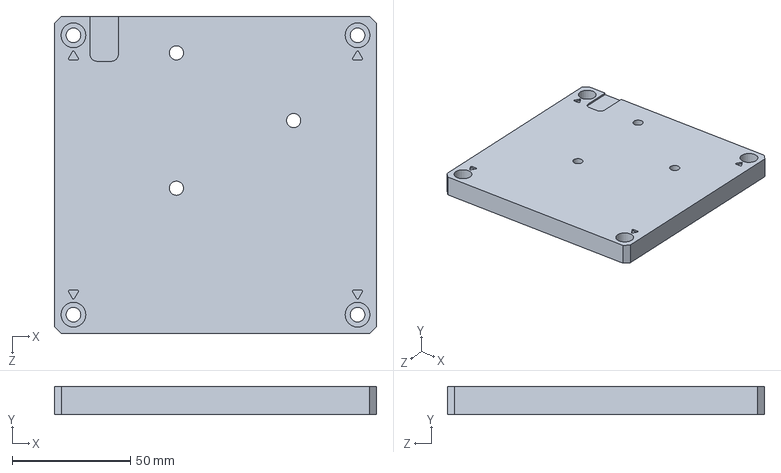
[picture p72: CAD file, 2024-07-01]
cad/モーターユニット架台プレート.SLDPRT
136.0 x 12.0 x 134.0 mm
