louislelay/Experimental-Equipment-for-Orthostatic-Exercise/cad/CB6-20.sldprt

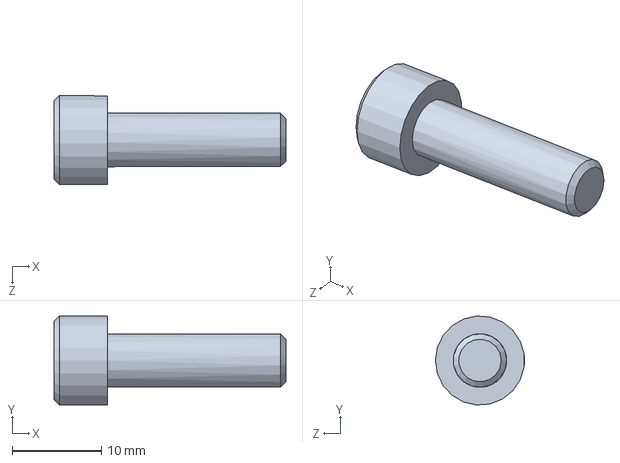
[picture p73: CAD file, 2024-07-01]
cad/CB6-20.sldprt
26.0 x 9.97 x 10.0 mm
