louislelay/Experimental-Equipment-for-Orthostatic-Exercise/cad/パネコート合板.SLDPRT

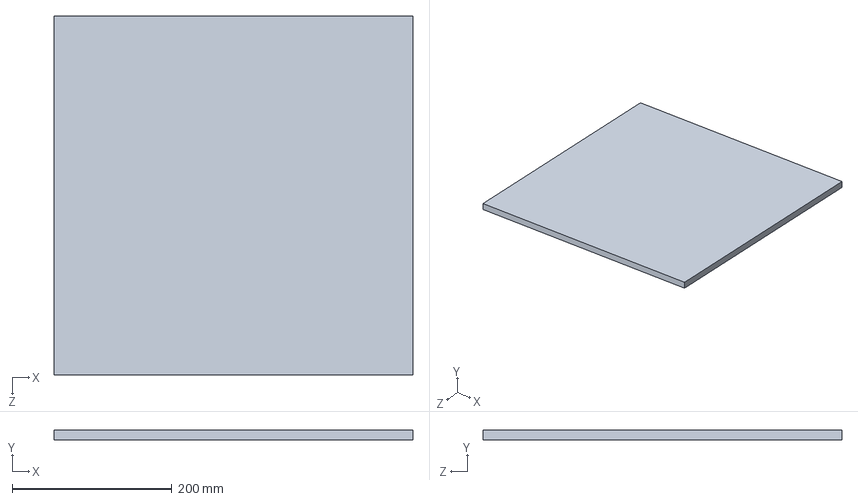
[picture p74: CAD file, 2024-07-01]
cad/パネコート合板.SLDPRT
450.0 x 12.0 x 450.0 mm
