louislelay/Experimental-Equipment-for-Orthostatic-Exercise/cad/中板.SLDPRT

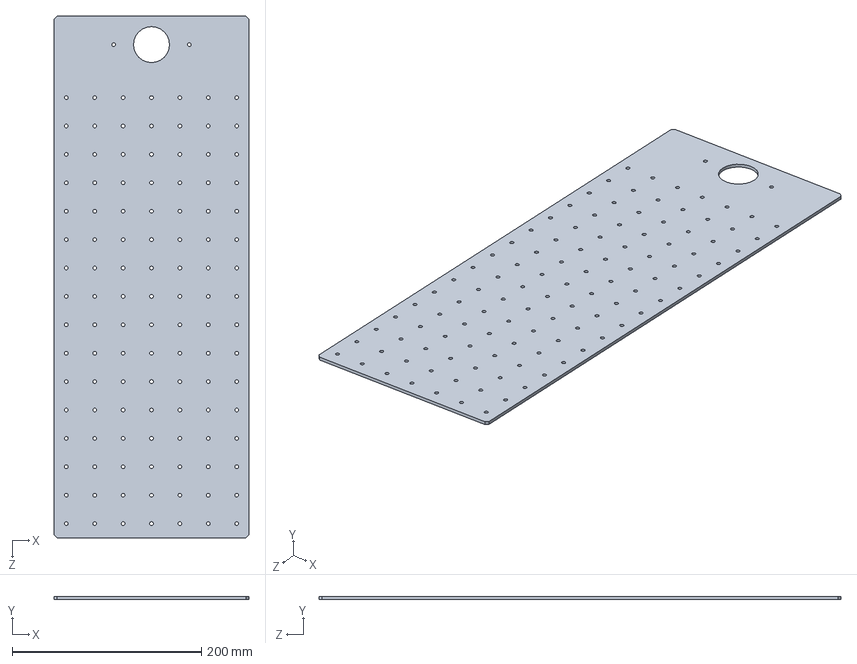
[picture p75: CAD file, 2024-07-01]
cad/中板.SLDPRT
206.0 x 3.20 x 551.0 mm
