louislelay/Experimental-Equipment-for-Orthostatic-Exercise/cad/TAP-K4-10.SLDPRT

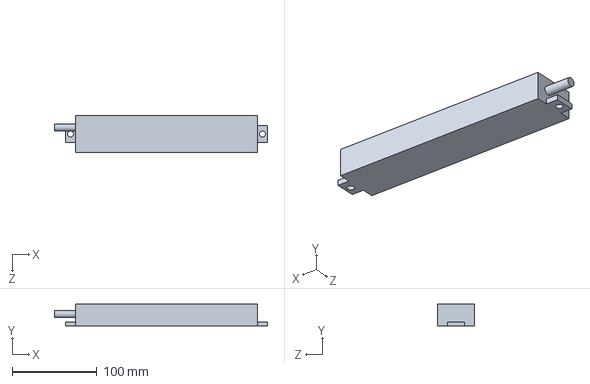
[picture p76: CAD file, 2024-07-01]
cad/TAP-K4-10.SLDPRT
252.0 x 26.0 x 43.5 mm
