louislelay/Experimental-Equipment-for-Orthostatic-Exercise/cad/コントローラ用マウンタ2.SLDPRT

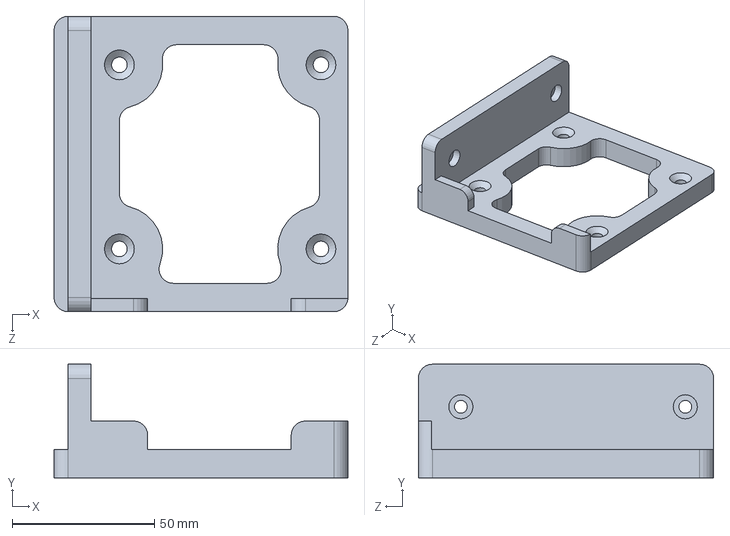
[picture p77: CAD file, 2024-07-01]
cad/コントローラ用マウンタ2.SLDPRT
103.5 x 40.0 x 104.0 mm
