louislelay/Experimental-Equipment-for-Orthostatic-Exercise/cad/KD-36-20-T_710.SLDPRT

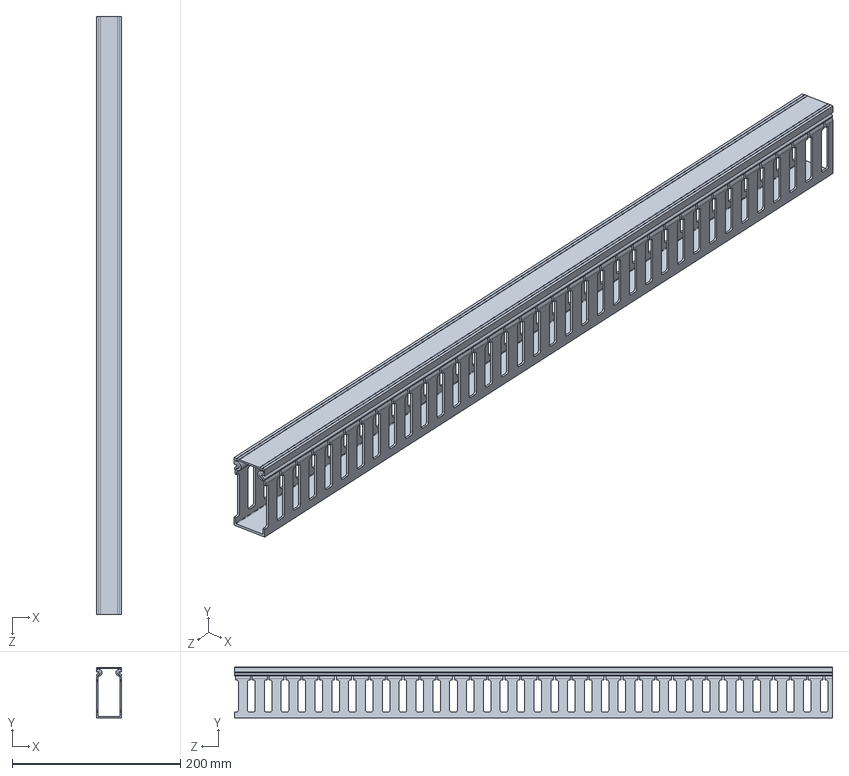
[picture p78: CAD file, 2024-07-01]
cad/KD-36-20-T_710.SLDPRT
30.0 x 60.2 x 710.0 mm
