louislelay/Experimental-Equipment-for-Orthostatic-Exercise/cad/サトーパーツ_K-29-6.1.SLDPRT

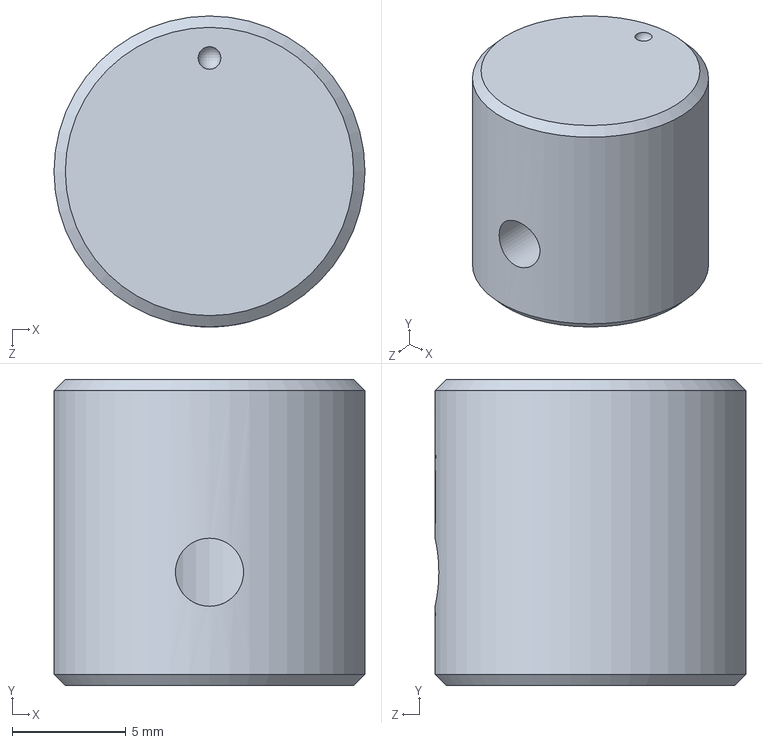
[picture p79: CAD file, 2024-07-01]
cad/サトーパーツ_K-29-6.1.SLDPRT
13.7 x 13.5 x 13.7 mm
