louislelay/Experimental-Equipment-for-Orthostatic-Exercise/cad/ユニバーサル基盤_9572b.SLDPRT

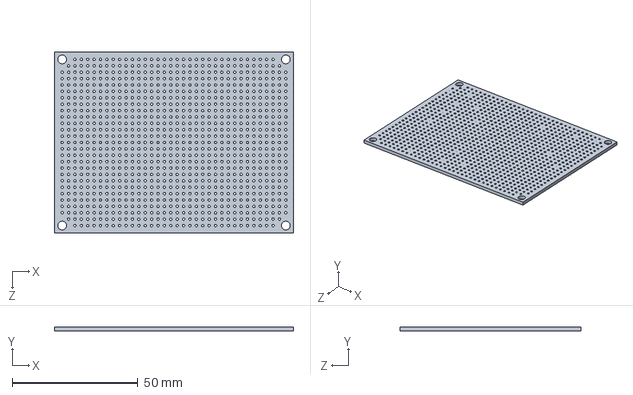
[picture p80: CAD file, 2024-07-01]
cad/ユニバーサル基盤_9572b.SLDPRT
95.0 x 1.60 x 72.0 mm
