louislelay/Experimental-Equipment-for-Orthostatic-Exercise/cad/CB6-12.sldprt

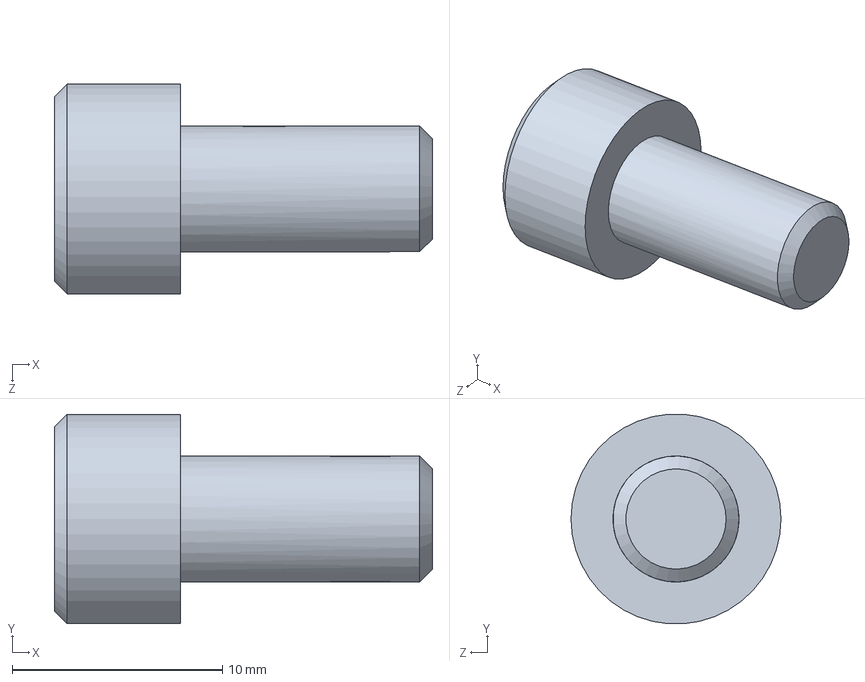
[picture p81: CAD file, 2024-07-01]
cad/CB6-12.sldprt
18.0 x 9.97 x 10.0 mm
