louislelay/Experimental-Equipment-for-Orthostatic-Exercise/cad/TAP-K4-10用ベース.SLDPRT

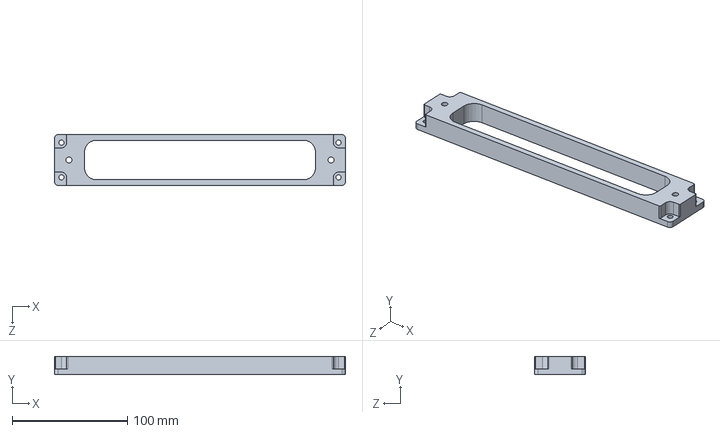
[picture p82: CAD file, 2024-07-01]
cad/TAP-K4-10用ベース.SLDPRT
252.0 x 16.0 x 44.0 mm
